Safecast/bGeigieZen/Misc documents  and software/SEO/What are the key benefits of using the bGeigieZen.pdf

The bGeigieZen offers several key benefits for educational settings:

These features make the bGeigieZen an excellent tool for enhancing STEM education and promoting hands-on, practical learning experiences in radiation monitoring and environmental science.

⁂

# What are the key benefits of using the bGeigieZen in educational settings

1. Practical learning tool: It serves as a hands-on device for teaching about radiation, nuclear science, and environmental monitoring in academic settings .
[1] [2]
2. Easy assembly: Students can build the device from a kit in about 30 minutes, providing a valuable learning experience in electronics and instrumentation .

[3]

3. Real-time data logging: The bGeigieZen can log radiation data in real-time using Wi-Fi, allowing students to collect and analyze environmental data quickly .

[3]

4. Open data sharing: It supports exporting data in formats compatible with Safecast's open data platforms, encouraging collaborative research and data analysis .

[1]

5. Versatile applications: The device can be used for various educational projects, from environmental monitoring to community science initiatives .

[1]

6. User-friendly interface: Its intuitive controls and clear IPS LCD display make it accessible to students of all experience levels .

[1]

7. Integration with online resources: Data can be easily visualized and interpreted using the Safecast API and online map, enhancing students' data analysis skills .

[3]

8. Customization potential: The open-source nature of the device allows for modification and integration into existing research infrastructures, promoting advanced learning opportunities .

[1]

9. Interdisciplinary learning: It combines elements of physics, environmental science, data analysis, and citizen science, fostering a multidisciplinary approach to education .
[1] [2]
10. Community engagement: The bGeigieZen can be used in community science projects, allowing students to participate in real-world environmental monitoring and contribute to collective safety data .

[1]

1. https://bgeigiezen.safecast.jp
2. https://safecast.org/devices/bgeigie-zen/

3. https://safecast.org/safecast-introduces-our-latest-open-source-geiger-counter-the-bgeigiezen/
