Safecast/bGeigieZen/Misc documents  and software/SEO/What role does the bGeigieZen play in educational.pdf

The bGeigieZen plays a significant role in educational programs at universities by serving as a versatile and practical tool for teaching and research in environmental science and radiation monitoring. Its contributions include:

By integrating the bGeigieZen into their educational programs, universities empower students with practical skills and contribute to broader scientific efforts in radiation safety and environmental stewardship.

⁂

# What role does the bGeigieZen play in educational programs at universities

1. Hands-on Learning: The bGeigieZen is used in laboratory courses where students can assemble the device from a kit, gaining practical experience in electronics, instrumentation, and radiation detection.
2. Teaching Radiation Science: It provides a tangible way to teach concepts of radiation, nuclear science, and environmental monitoring, making abstract theories more accessible through real-world applications.
3. Fieldwork and Data Collection: With its GPS integration and real-time data logging capabilities, the device allows students to conduct field studies, collect radiation data, and map environmental conditions.
4. Interdisciplinary Applications: The bGeigieZen supports interdisciplinary learning by combining elements of physics, environmental science, data analysis, and citizen science into academic programs.
5. Open-Source Collaboration: Universities can leverage Safecast's open-source platform to share data and collaborate on global environmental monitoring projects, fostering a sense of community-driven science.
6. Research Projects: It is used in university-led research initiatives, such as studying radioactive contamination or assessing environmental safety around nuclear facilities.
7. Curriculum Integration: The device is incorporated into courses and workshops focused on environmental monitoring, promoting active learning and critical thinking among students.
