Safecast/bGeigieZen/Misc documents  and software/bGeigieZen  info.docx

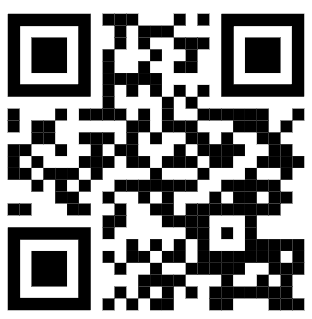
[picture p9: figure]

bGeigieZen information:

Version :V4.0.6

ID :5053

For more information visit

https://t.ly/_J40M
