Safecast/bGeigieZen/Misc documents  and software/safecast QR code sticker.docx

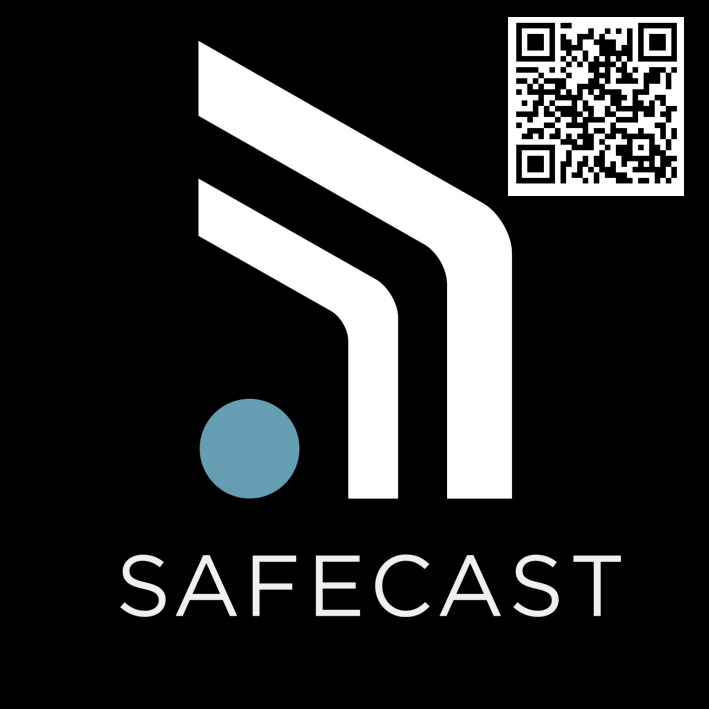
[picture p10: figure]
