Safecast/bGeigieZen/Misc documents  and software/2024-03-05 Zen sticker for brother QL700 between liner and case..docx

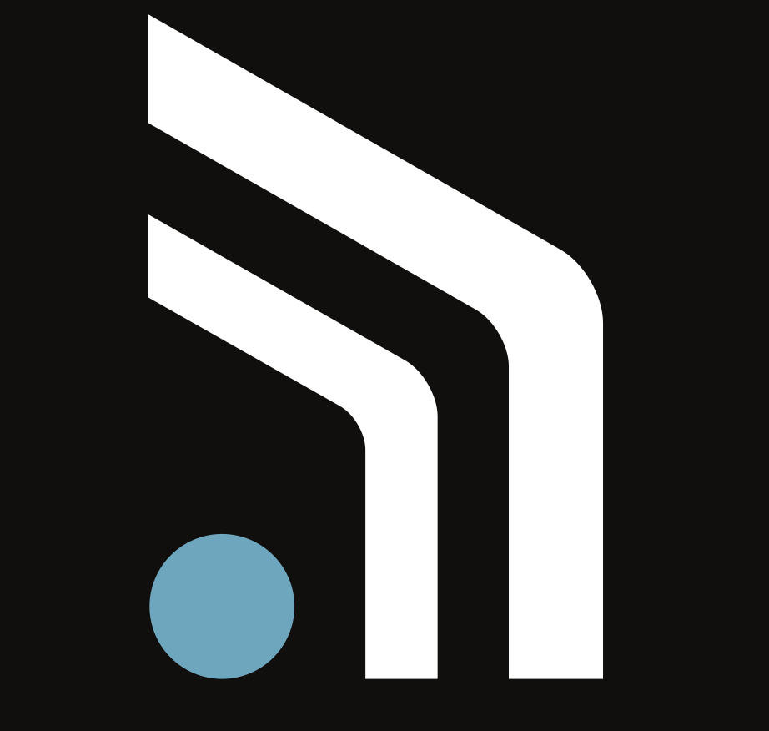
[picture p11: figure]
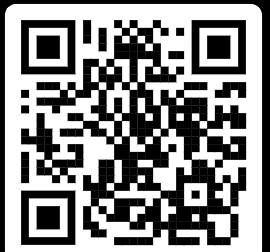
[picture p12: figure]

SAFECAST
