Safecast/bGeigieZen/Misc documents  and software/2024-03-05 Zen inside lines.docx

〒633-1302 奈良

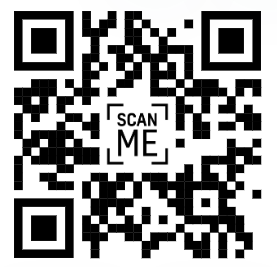
[picture p13: figure]

県宇陀郡御杖村菅野616

616 Sugano, (https://www.google.com/maps/place/YR-DESIGN/@34.482597,136.163349,4319m/data=!3m1!1e3!4m5!3m4!1s0x0:0x89b70d0ed6831661!8m2!3d34.482597!4d136.163349)

Mitsue-Village, Uda District, Nara, 633-1302 Japan (https://www.google.com/maps/place/YR-DESIGN/@34.482597,136.163349,4319m/data=!3m1!1e3!4m5!3m4!1s0x0:0x89b70d0ed6831661!8m2!3d34.482597!4d136.163349)
