Safecast/bGeigieZen/Misc documents  and software/SEO/How can universities integrate the bGeigieZen into.pdf

Universities can integrate the bGeigieZen into their environmental monitoring programs in several effective ways:

# How can universities integrate the bGeigieZen into their environmental monitoring programs

Research Projects

1. Conduct long-term radiation monitoring studies across campus and surrounding areas, creating detailed radiation maps over time .
[1] [2]
2. Use the device in interdisciplinary research projects combining environmental science, physics, and data analysis.

Curriculum Integration

1. Incorporate the bGeigieZen into laboratory courses for hands-on experience with radiation detection and environmental monitoring .

[2]

2. Develop practical exercises where students assemble the device from a kit, enhancing their understanding of instrumentation .

[1]

Community Science Initiatives

1. Engage students in citizen science projects, contributing data to Safecast's open platforms and fostering community involvement .

[2]

2. Collaborate with local communities to monitor radiation levels, promoting environmental awareness and stewardship.

Data Analysis and Visualization

1. Utilize the bGeigieZen's real-time data logging capabilities to teach students about data collection, analysis, and interpretation .

[1]

2. Integrate collected data with the Safecast API and online map for advanced data visualization exercises .

[1]

Emergency Preparedness

1. Include the bGeigieZen in emergency response training programs for campus safety personnel .

[2]

2. Establish a network of fixed bGeigieZen sensors across campus for continuous environmental monitoring .

[1]

By implementing these strategies, universities can leverage the bGeigieZen's capabilities to enhance their environmental monitoring programs, providing students with valuable hands-on experience and contributing to broader scientific understanding of radiation levels in their local environment.

⁂

1. https://safecast.org/safecast-introduces-our-latest-open-source-geiger-counter-the-bgeigiezen/
2. https://safecast.org/devices/bgeigie-zen/
