Safecast/bGeigieZen/bgeigie_firmware_pio/images/Screenshot from 2022-03-10 14-36-16 Robin sample wifi implementaion.png

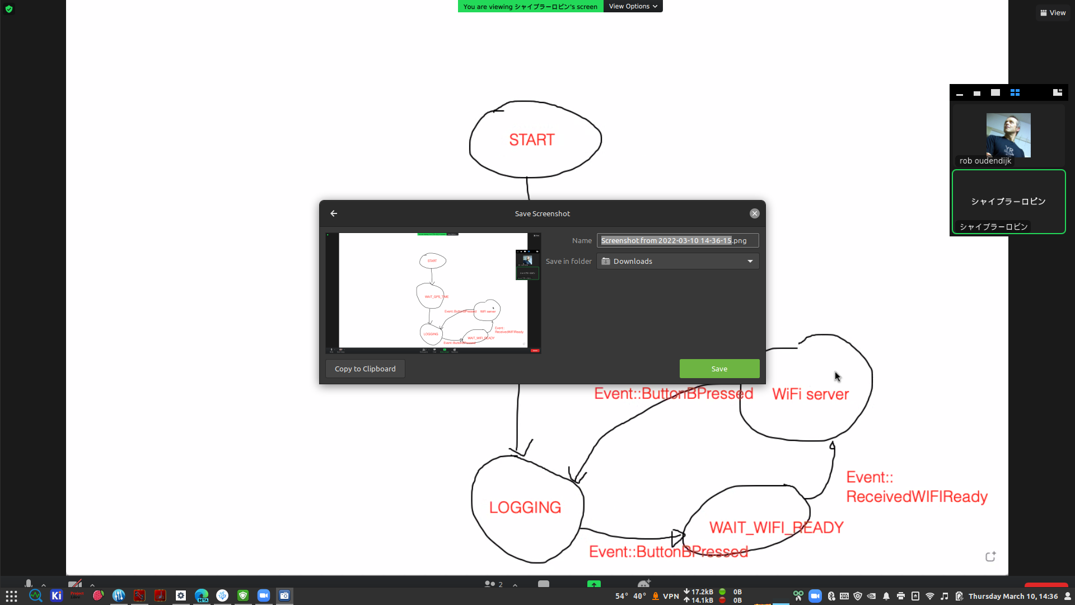
bgeigie_firmware_pio/images/Screenshot from 2022-03-10 14-36-16 Robin sample wifi implementaion.png
