Safecast/bGeigieZen/designs/concept.png

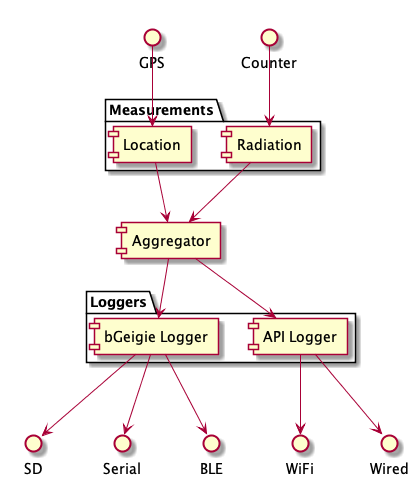
designs/concept.png
