Safecast/bGeigieZen/designs/design_idea.png

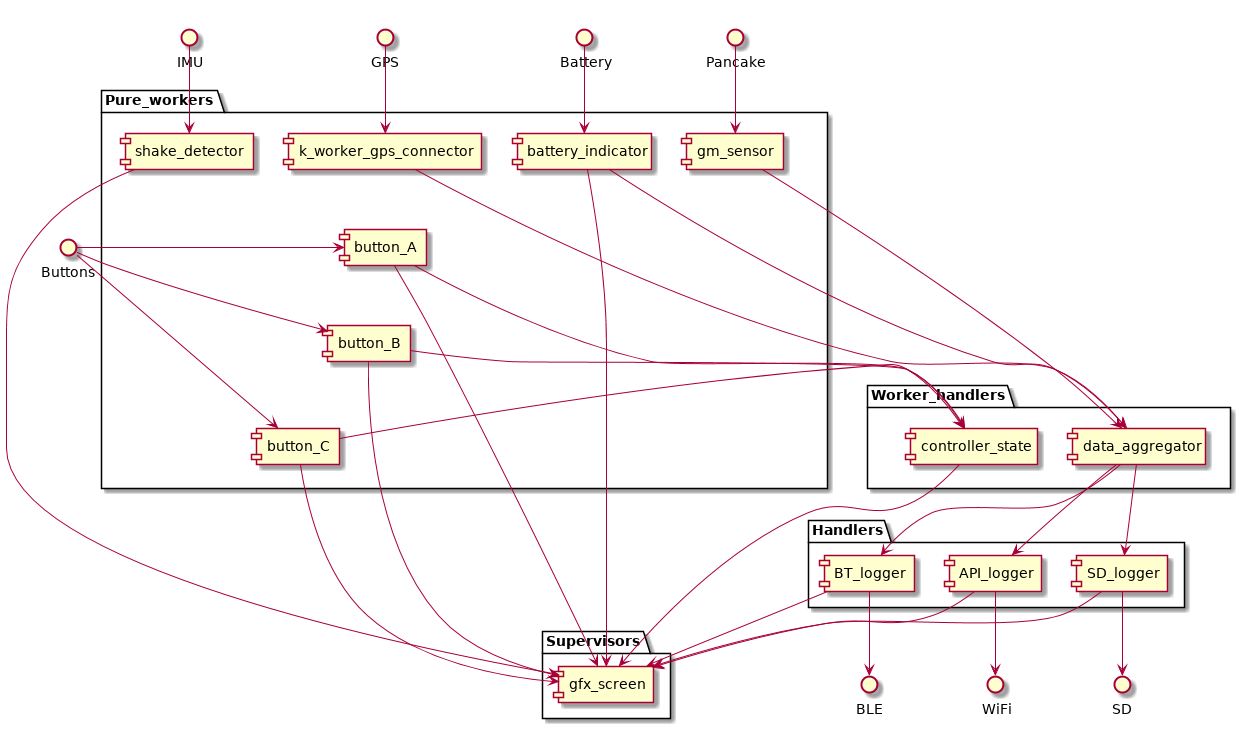
designs/design_idea.png
