Safecast/bGeigieZen/designs/Idea for rotating text.png

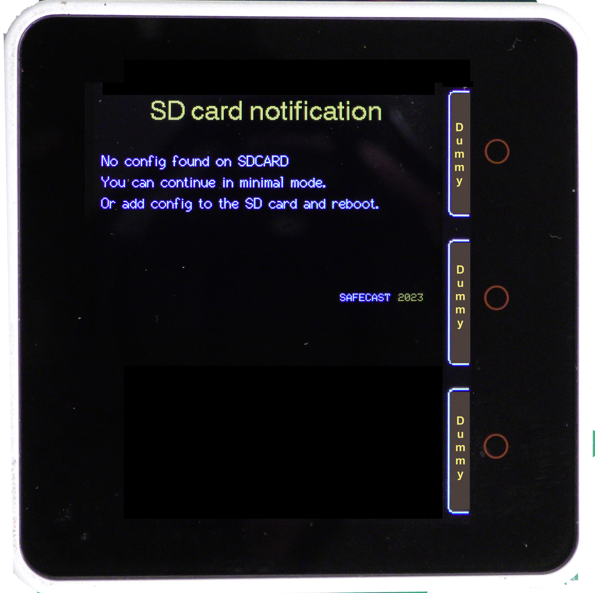
designs/Idea for rotating text.png
