Safecast/bGeigieZen/Misc documents  and software/436710781_377460041415420_154169997321250752_n.jpg

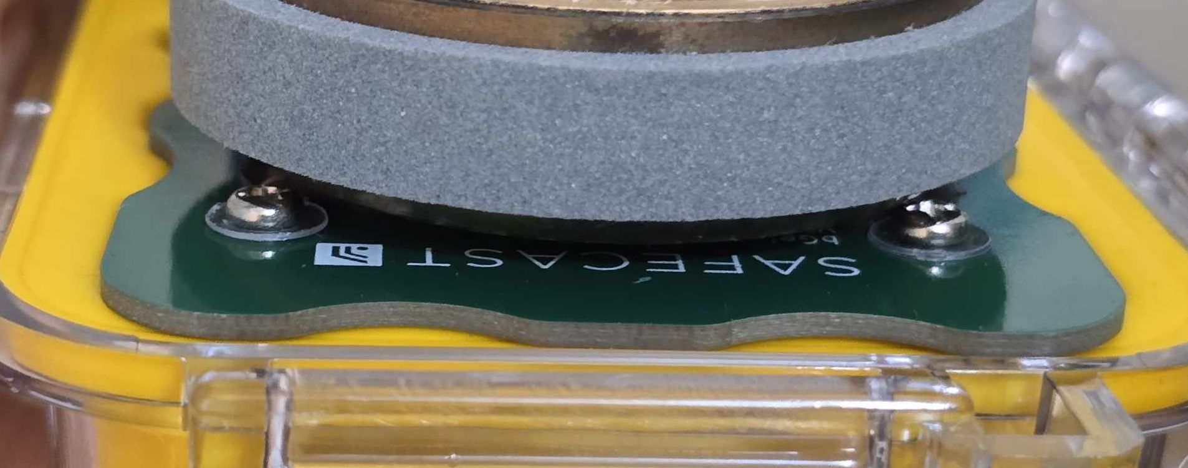
Misc documents and software/436710781_377460041415420_154169997321250752_n.jpg
