Safecast/bGeigieZen/Misc documents  and software/buttons sticker Zen.png

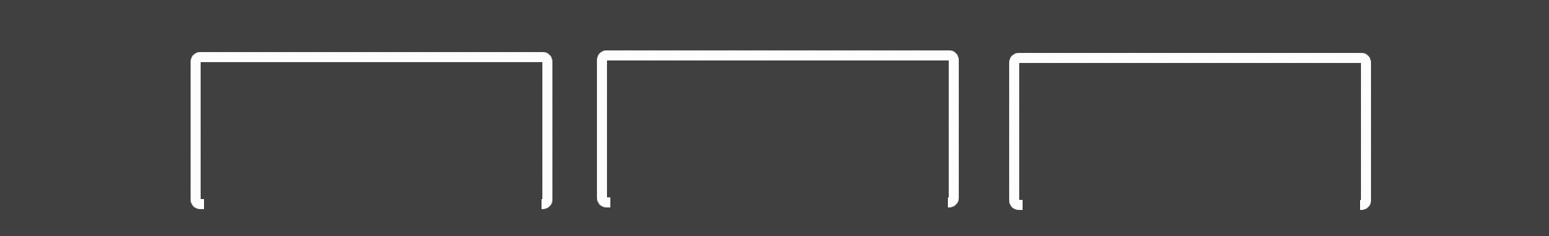
Misc documents and software/buttons sticker Zen.png
