Safecast/bGeigieZen/Misc documents  and software/Editor _ Mermaid Chart-2025-06-17-123522.png

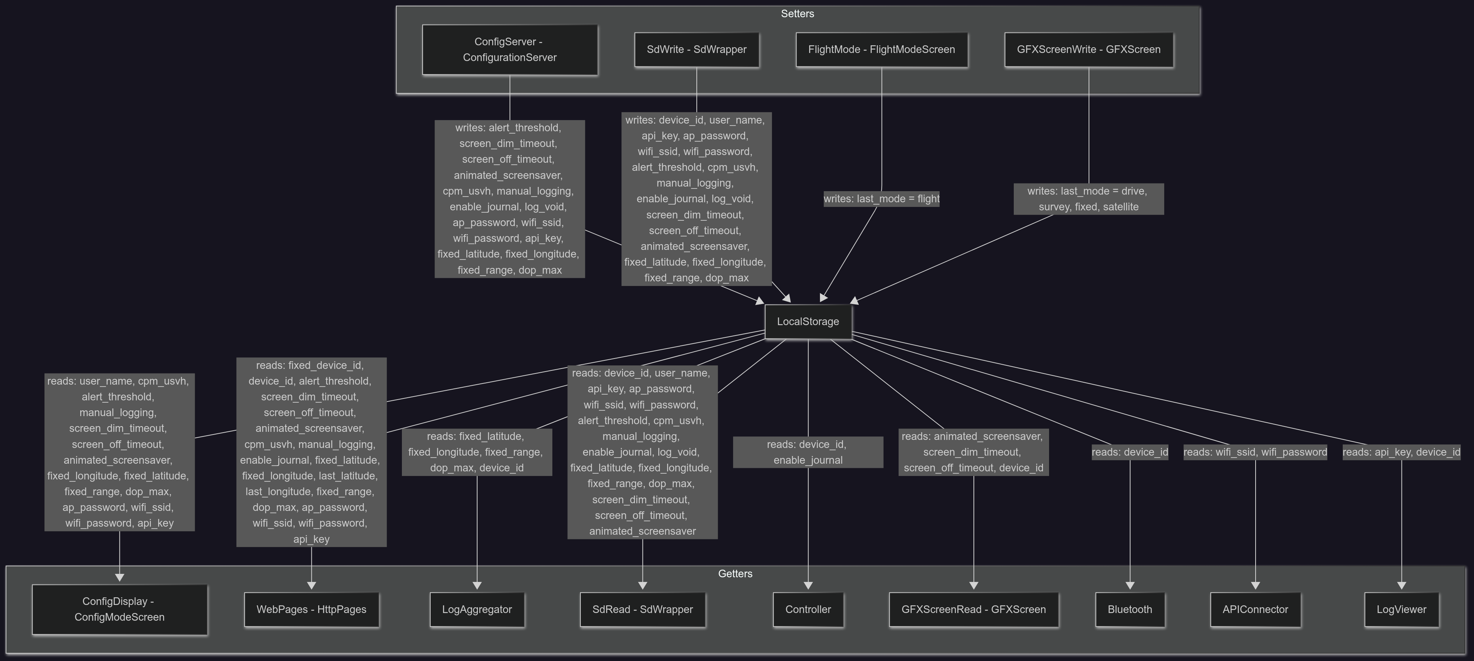
Misc documents and software/Editor _ Mermaid Chart-2025-06-17-123522.png
