Safecast/bGeigieZen/Misc documents  and software/Editor _ Mermaid Chart-2025-06-18-021637.png

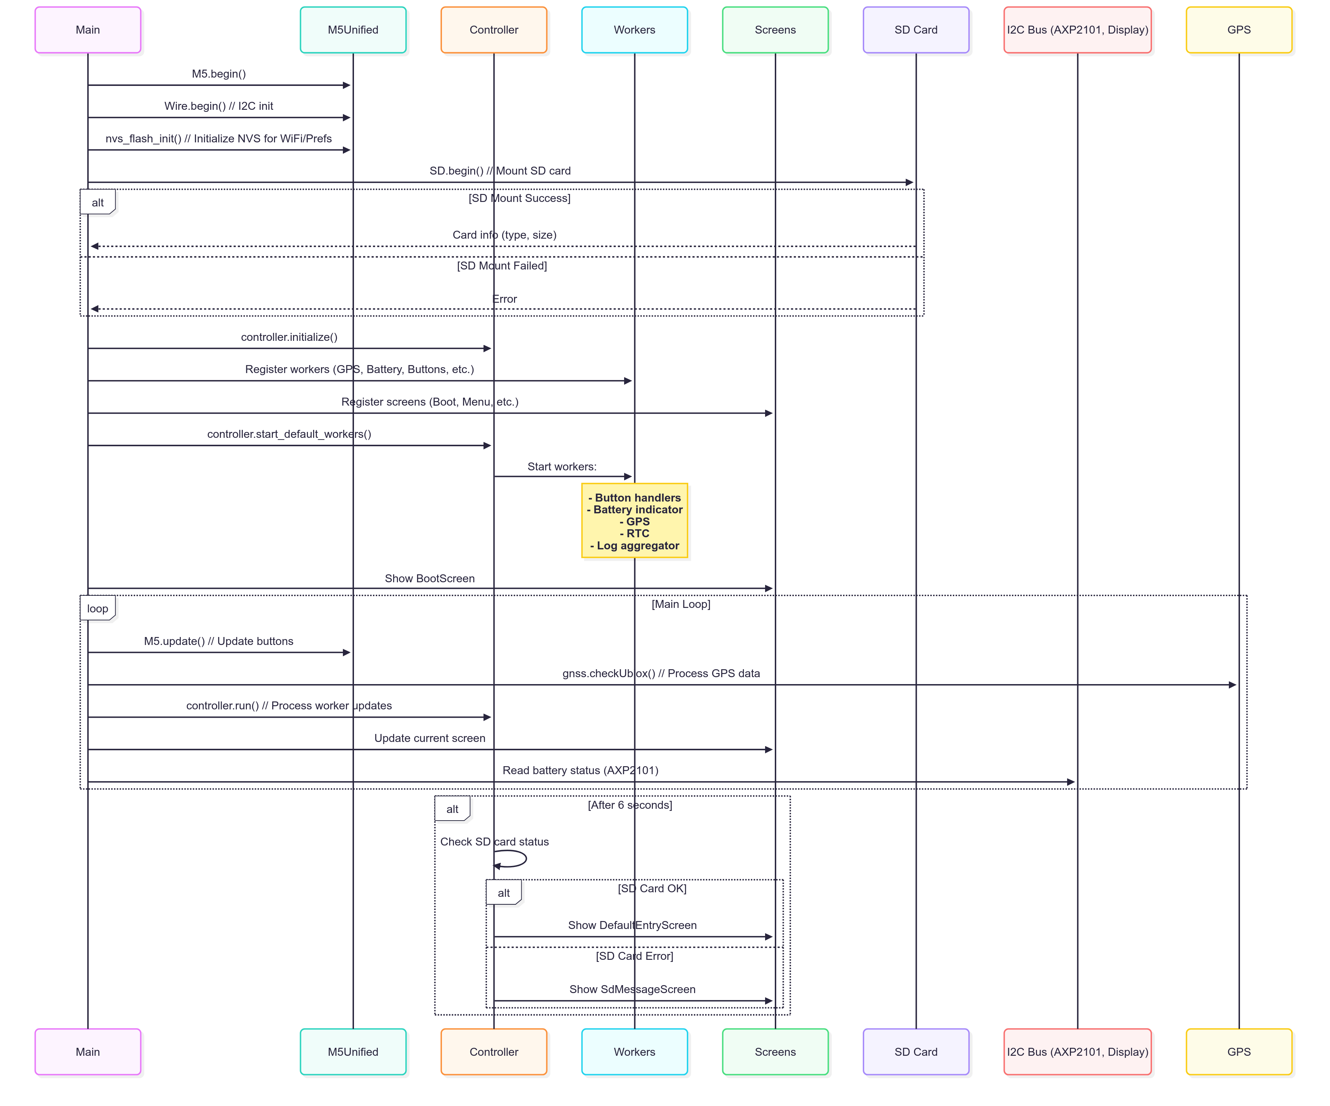
Misc documents and software/Editor _ Mermaid Chart-2025-06-18-021637.png
