Safecast/bGeigieZen/Misc documents  and software/Images /3006.jpg

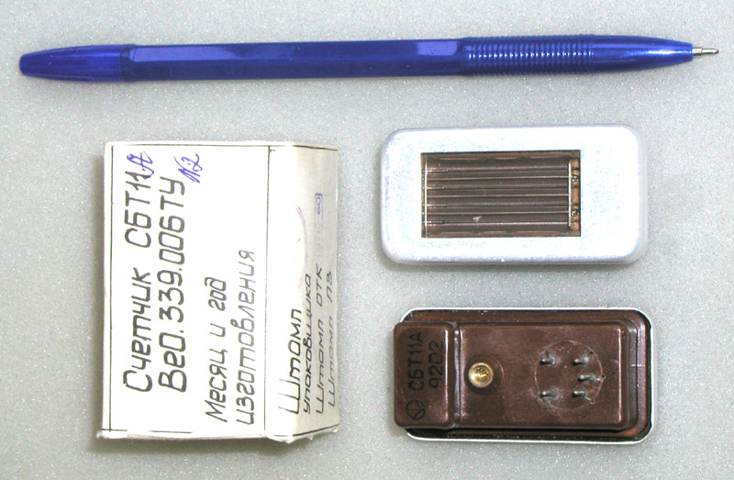
Misc documents and software/Images /3006.jpg
