Safecast/bGeigieZen/Misc documents  and software/Images /3006_1.gif

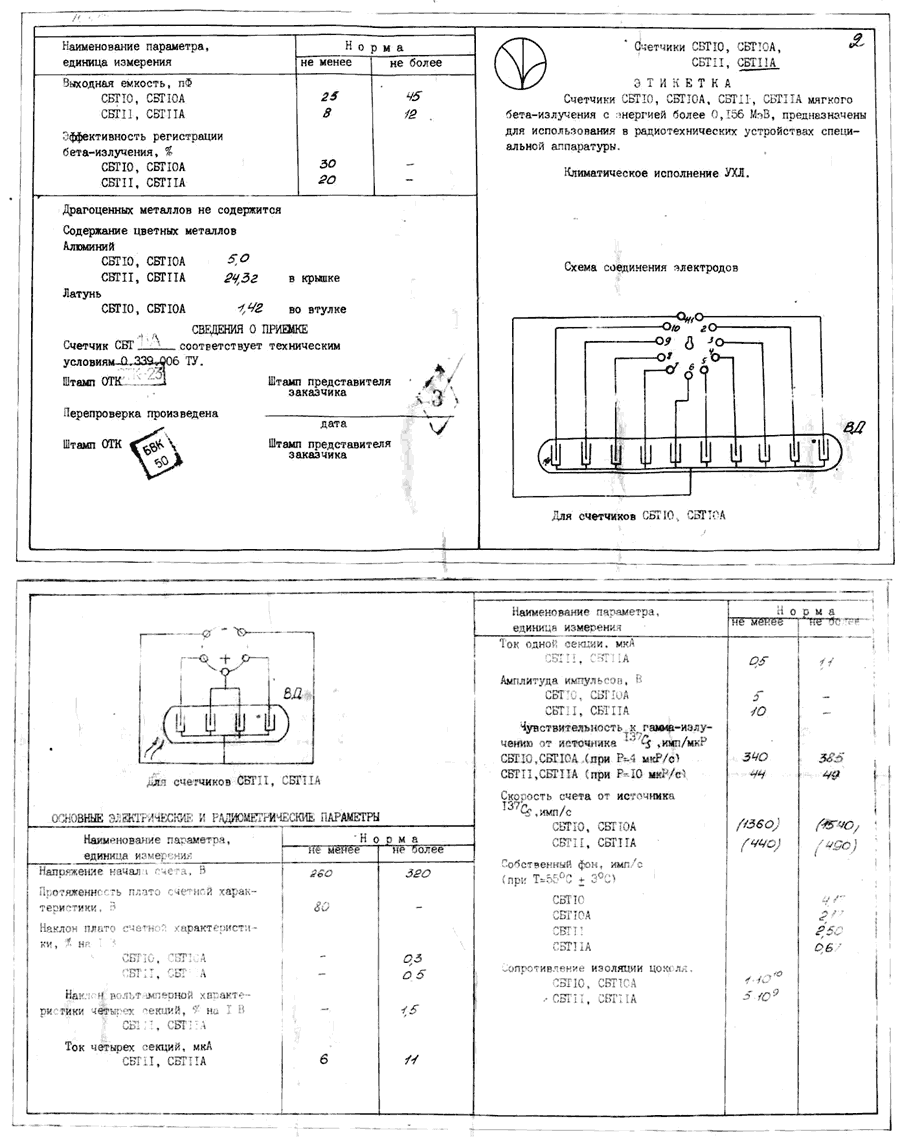
Misc documents and software/Images /3006_1.gif
