Safecast/bGeigieZen/Misc documents  and software/Images /SBT-11A data sheet.jpg

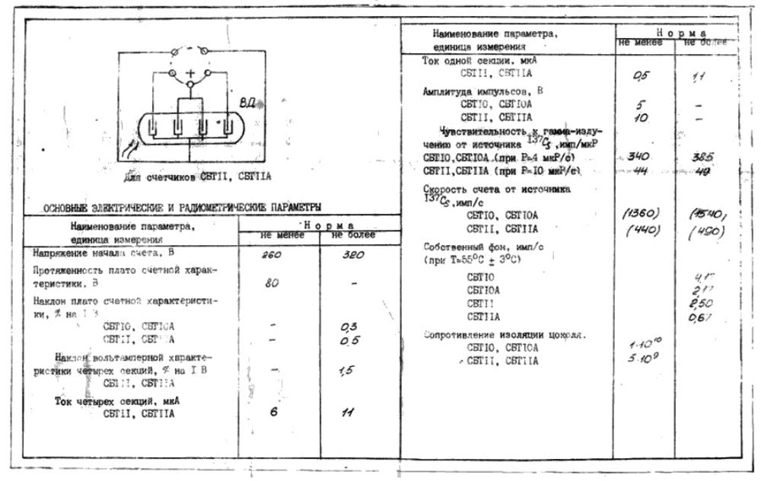
Misc documents and software/Images /SBT-11A data sheet.jpg
