Safecast/bGeigieZen/Misc documents  and software/Images/Screenshot from 2024-03-13 09-20-50.png

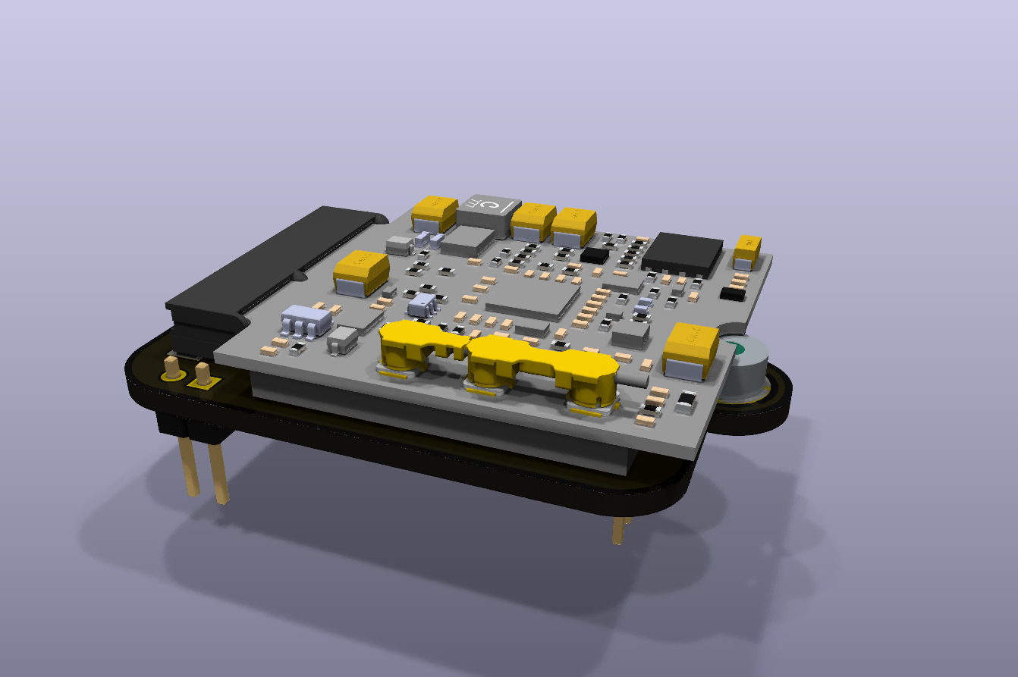
Misc documents and software/Images/Screenshot from 2024-03-13 09-20-50.png
