Safecast/bGeigieZen/Misc documents  and software/Images/Screenshot from 2024-03-13 09-23-09.png

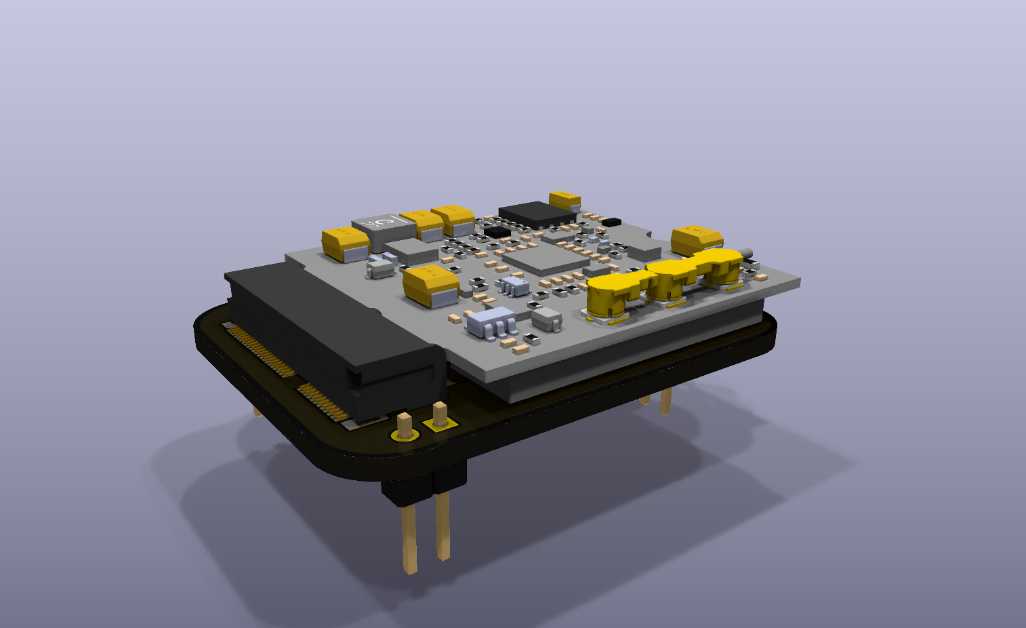
Misc documents and software/Images/Screenshot from 2024-03-13 09-23-09.png
