Safecast/bGeigieZen/Misc documents  and software/IMG_1486.jpg

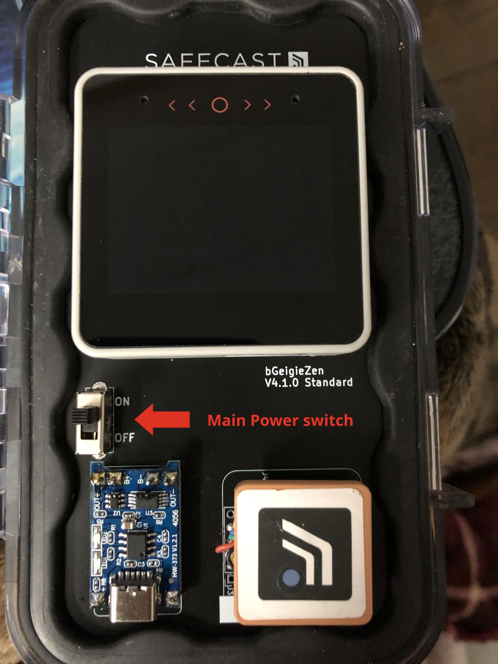
Misc documents and software/IMG_1486.jpg
