Safecast/bGeigieZen/Misc documents  and software/IMG_1487.jpg

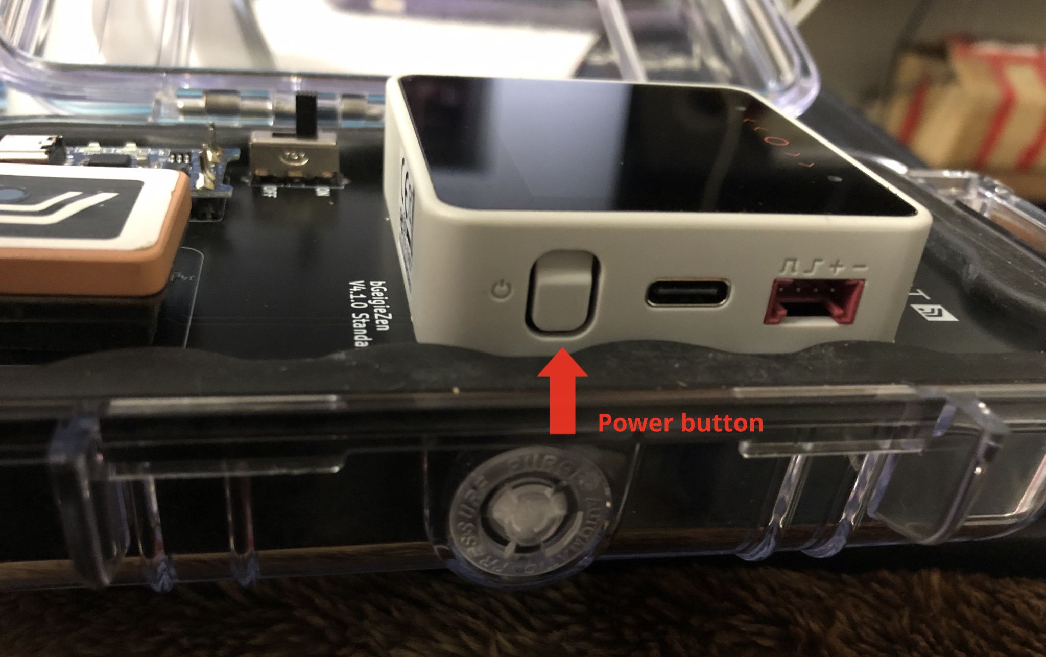
Misc documents and software/IMG_1487.jpg
