Safecast/bGeigieZen/Misc documents  and software/IMG_1488.jpg

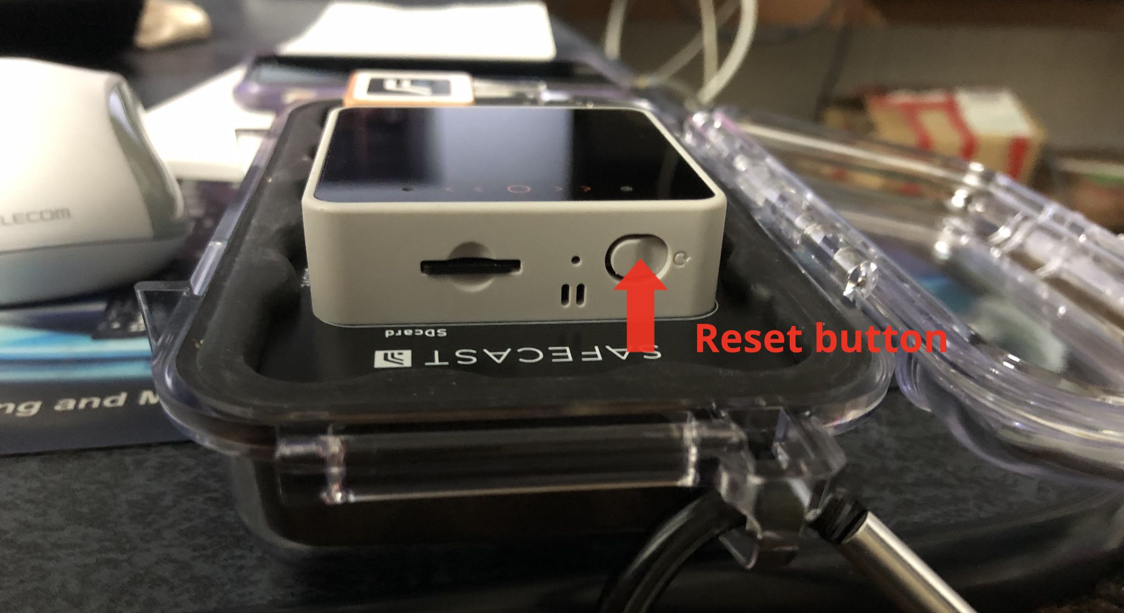
Misc documents and software/IMG_1488.jpg
