Safecast/bGeigieZen/Misc documents  and software/LND 7317 grids invoice from Louis.png

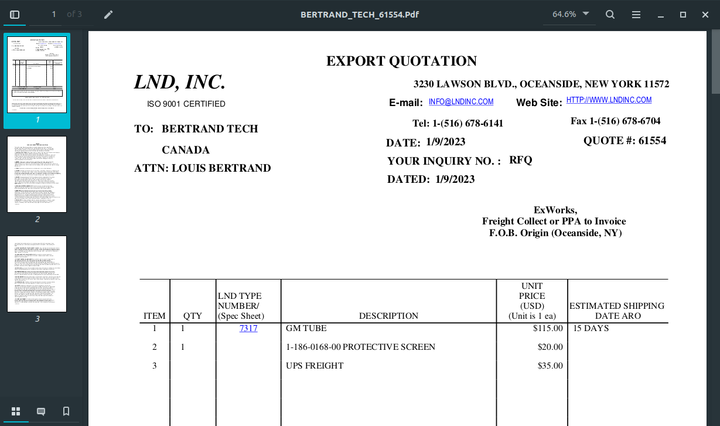
Misc documents and software/LND 7317 grids invoice from Louis.png
