Safecast/bGeigieZen/Misc documents  and software/Vertical timeline nano-zen.png

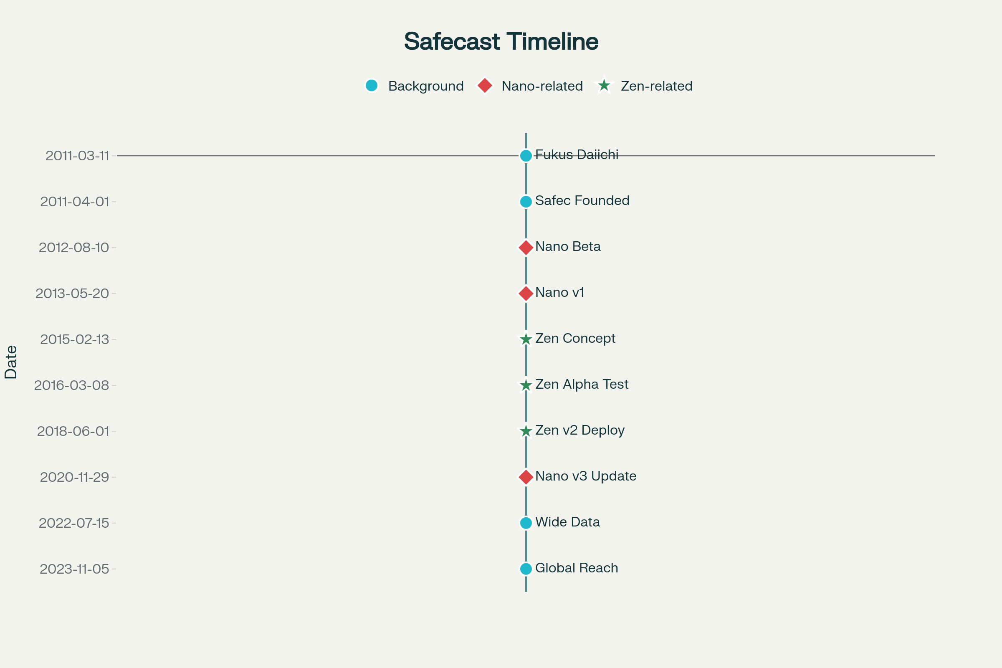
Misc documents and software/Vertical timeline nano-zen.png
