Safecast/bGeigieZen/Misc documents  and software/3d models/pelican 1040-cradle slide mold.stl

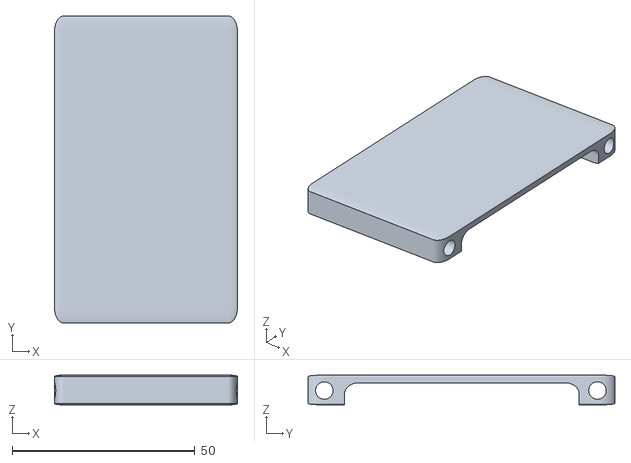
[picture p49: CAD file, 2024-11-16]
Misc documents and software/3d models/pelican 1040-cradle slide mold.stl
50.1 x 84.0 x 8.17
