Safecast/bGeigieZen/hardware/bGeigieZen V4.x.x draft and production/bGeigieZen V4.2.x/ GPS for  4.1.0 aNFW .stl

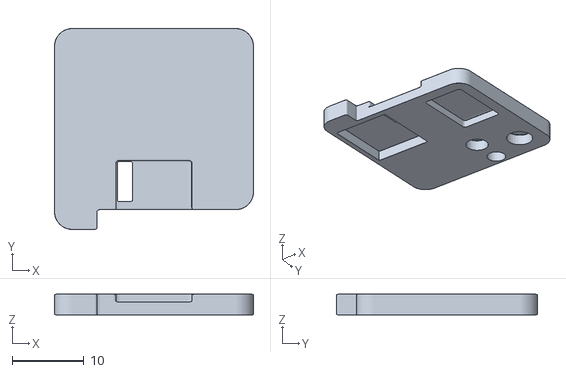
[picture p50: CAD file, 2024-12-10]
hardware/bGeigieZen V4.x.x draft and production/bGeigieZen V4.2.x/ GPS for 4.1.0 aNFW .stl
27.8 x 28.1 x 2.87
