Safecast/bGeigieZen/hardware/bGeigieZen V4.x.x draft and production/bGeigieZen V4.2.x/shapes3D/3557-2.step

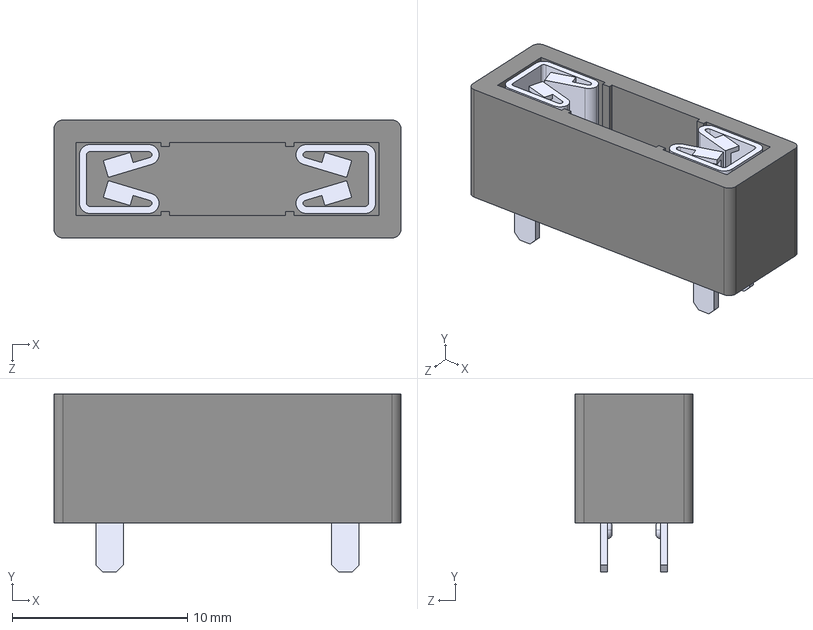
[picture p51: CAD file, 2024-08-04]
hardware/bGeigieZen V4.x.x draft and production/bGeigieZen V4.2.x/shapes3D/3557-2.step
19.8 x 10.2 x 6.73 mm
