Safecast/bGeigieZen/Misc documents  and software/3d models/pelican 1040-cradle making case mold-2b.stl

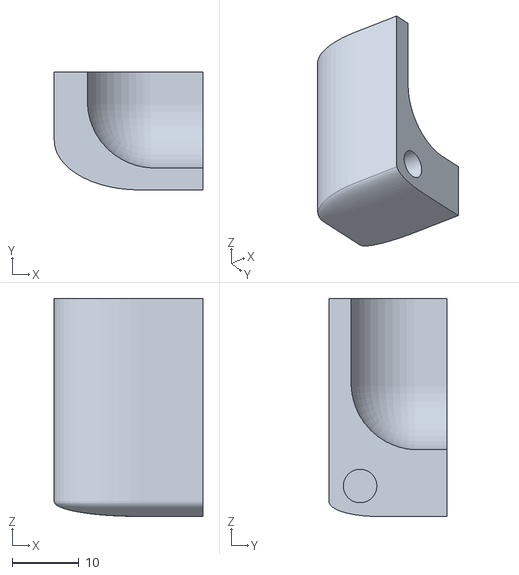
[picture p52: CAD file, 2024-10-24]
Misc documents and software/3d models/pelican 1040-cradle making case mold-2b.stl
22.2 x 17.6 x 32.6
