Safecast/bGeigieZen/hardware/bGeigieZen V4.x.x draft and production/bGeigieZen V4.2.x/ GPS for  4.0.9 NFW .stl

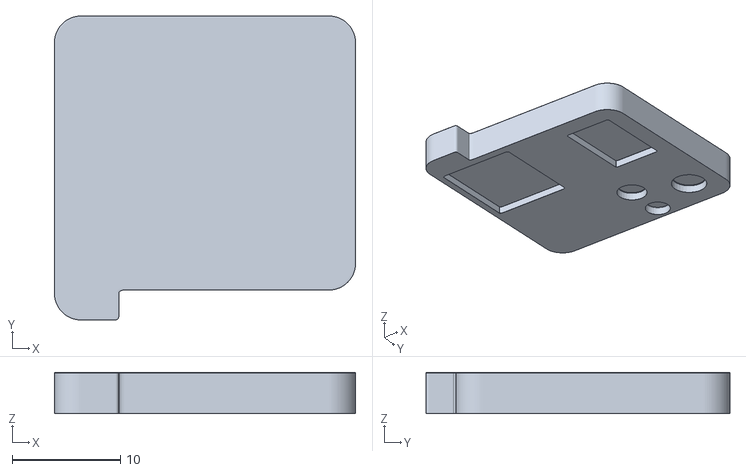
[picture p53: CAD file, 2024-12-10]
hardware/bGeigieZen V4.x.x draft and production/bGeigieZen V4.2.x/ GPS for 4.0.9 NFW .stl
27.8 x 28.1 x 3.79
