Safecast/bGeigieZen/Misc documents  and software/3d models/pelican 1040-cradle QI sled A.stl

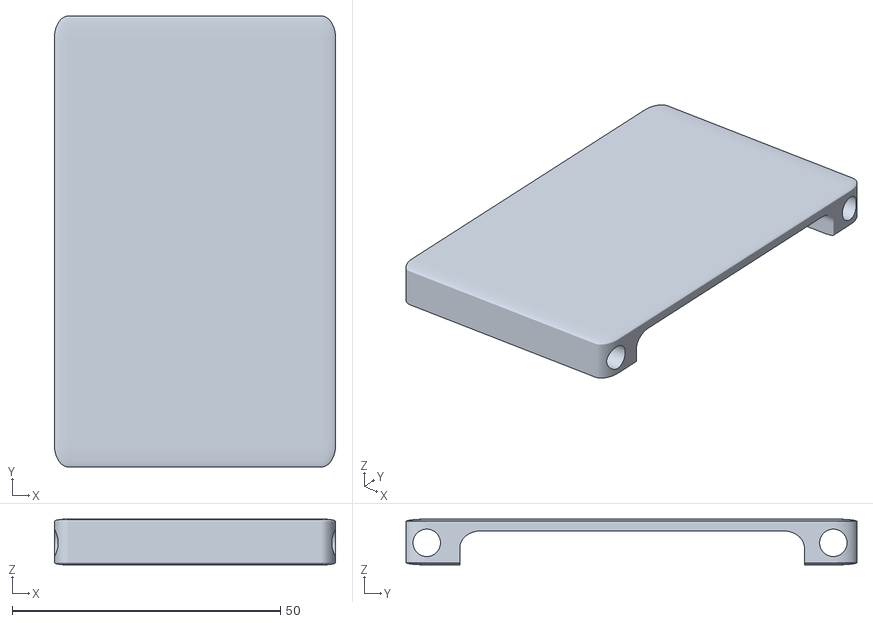
[picture p54: CAD file, 2024-10-24]
Misc documents and software/3d models/pelican 1040-cradle QI sled A.stl
52.4 x 84.0 x 8.55
