Safecast/bGeigieZen/hardware/bGeigieZen V4.x.x draft and production/bGeigieZen V4.2.x/shapes3D/Charging Module TP4057 Mini.step

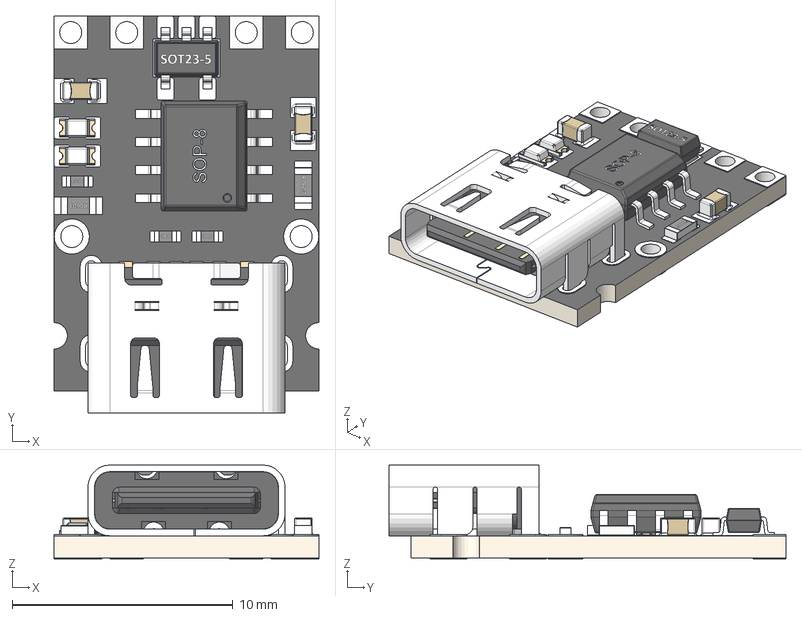
[picture p55: CAD file, 2024-05-21]
hardware/bGeigieZen V4.x.x draft and production/bGeigieZen V4.2.x/shapes3D/Charging Module TP4057 Mini.step
12.0 x 18.0 x 4.26 mm
USB C 6P SMD Female
SOP-8
0603LEDO
0603LEDR
Pin1 x 2
Pin2 x 2
CeramicBody x 2
SOT23-5 V1
R0603 x 2
R0402 x 3
