Safecast/bGeigieZen/Misc documents  and software/3d models/pelican 1040-cradle making case mold-2a.stl

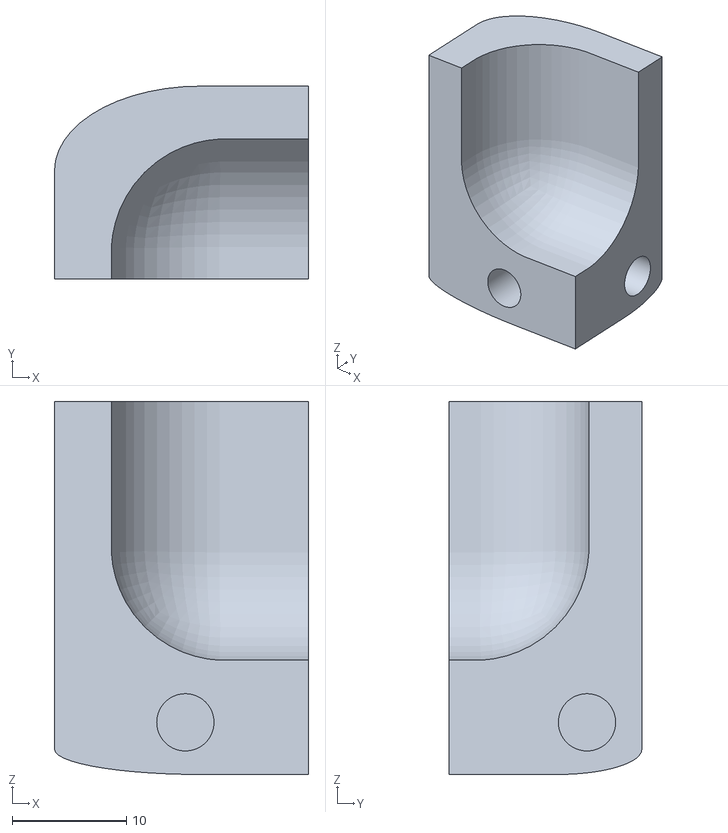
[picture p56: CAD file, 2024-10-24]
Misc documents and software/3d models/pelican 1040-cradle making case mold-2a.stl
22.2 x 16.8 x 32.6
