Safecast/bGeigieZen/Misc documents  and software/3d models/pelican 1040-cradle making case mold-2d.stl

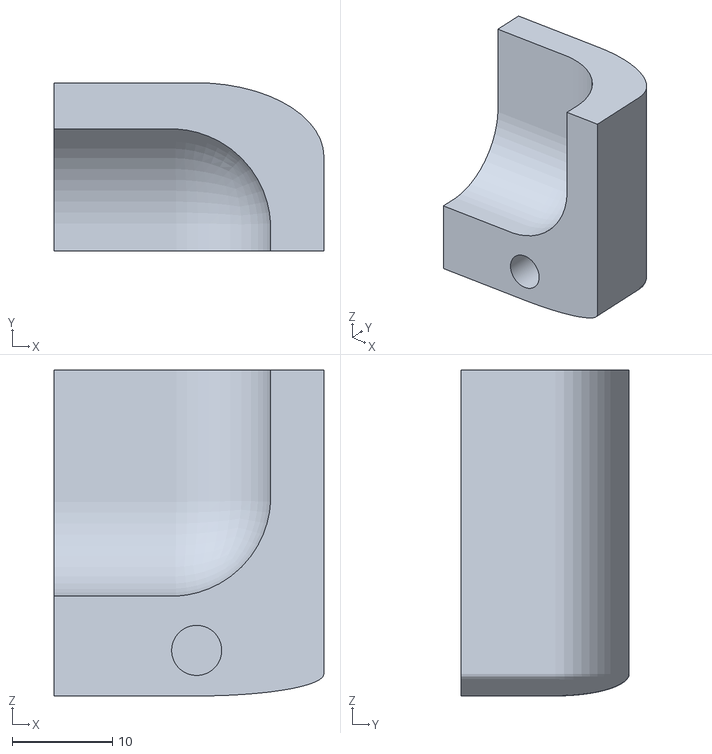
[picture p59: CAD file, 2024-10-24]
Misc documents and software/3d models/pelican 1040-cradle making case mold-2d.stl
27.0 x 16.8 x 32.6
