Safecast/bGeigieZen/hardware/bGeigieZen V4.x.x draft and production/bGeigieZen V4.2.x/shapes3D/LIGHT_UNIT.stp

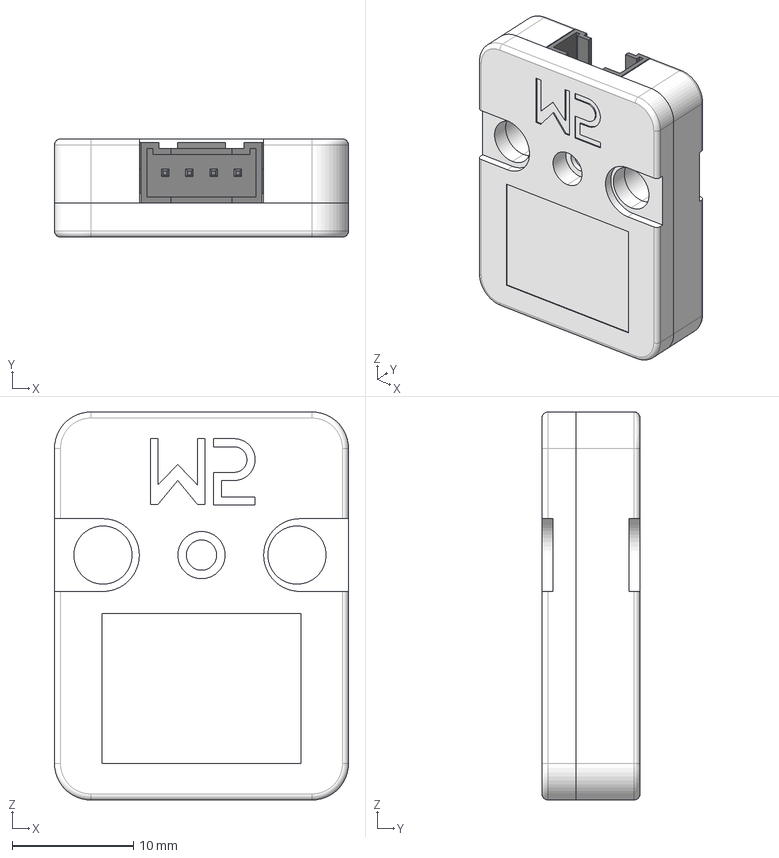
[picture p60: CAD file, 2023-09-07]
hardware/bGeigieZen V4.x.x draft and production/bGeigieZen V4.2.x/shapes3D/LIGHT_UNIT.stp
24.2 x 8.10 x 32.0 mm
M5STACK_LIGHT_UNIT-prt0
M5STACK_LIGHT_UNIT-prt1
M5STACK_LIGHT_UNIT-prt2
M5STACK_LIGHT_UNIT-prt3
M5STACK_LIGHT_UNIT-prt4
M5STACK_LIGHT_UNIT-prt5
M5STACK_LIGHT_UNIT-prt6
M5STACK_LIGHT_UNIT-prt7
M5STACK_LIGHT_UNIT-prt8
