Safecast/bGeigieZen/Misc documents  and software/3d models/plate core1 for NFW and standard.stl

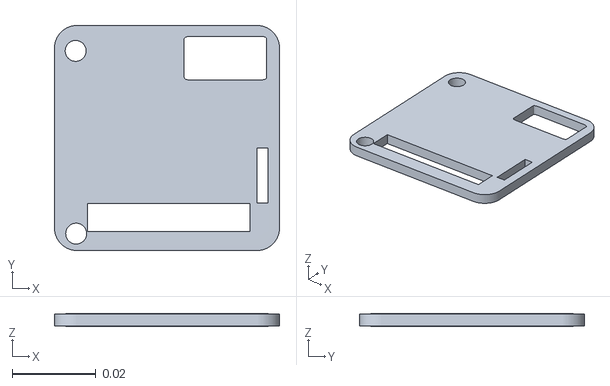
[picture p61: CAD file, 2024-10-21]
Misc documents and software/3d models/plate core1 for NFW and standard.stl
0.0538 x 0.0538 x 0.003
