Safecast/bGeigieZen/hardware/bGeigieZen V4.x.x draft and production/bGeigieZen V4.2.x/shapes3D/qwiic.STEP

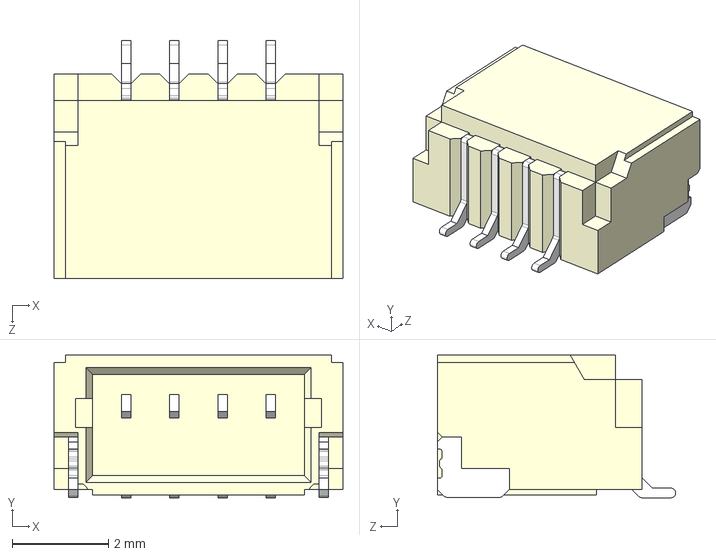
[picture p62: CAD file, 2022-01-05]
hardware/bGeigieZen V4.x.x draft and production/bGeigieZen V4.2.x/shapes3D/qwiic.STEP
6.00 x 2.96 x 4.95 mm
