Safecast/bGeigieZen/Misc documents  and software/3d models/Zen cradle rought making case.stl

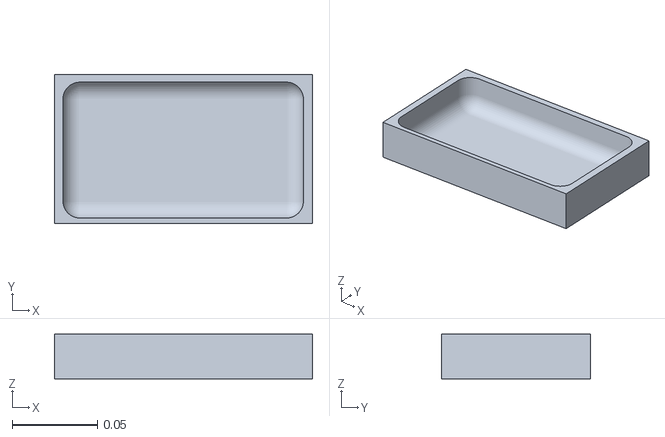
[picture p63: CAD file, 2024-10-21]
Misc documents and software/3d models/Zen cradle rought making case.stl
0.151 x 0.0877 x 0.0262
