Safecast/bGeigieZen/hardware/bGeigieZen V4.x.x draft and production/bGeigieZen V4.2.x/shapes3D/QWIIC-SM04B-SRSS-TB(LF)(SN).stl

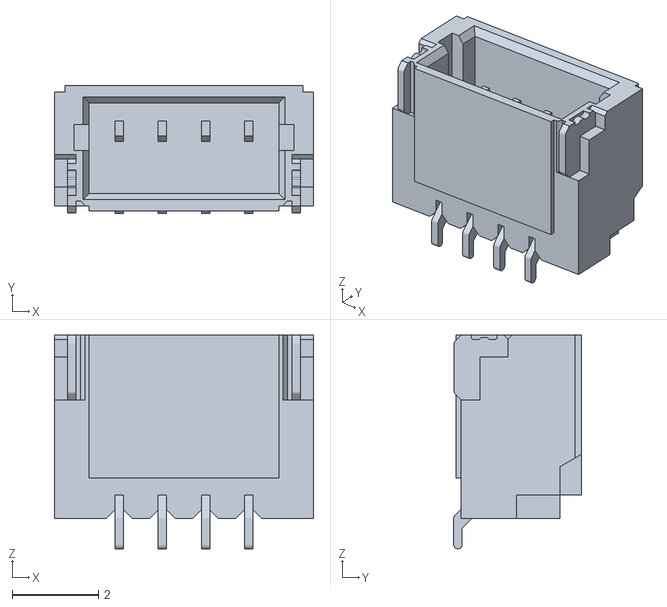
[picture p64: CAD file, 2022-01-05]
hardware/bGeigieZen V4.x.x draft and production/bGeigieZen V4.2.x/shapes3D/QWIIC-SM04B-SRSS-TB(LF)(SN).stl
6.00 x 2.96 x 4.95
