Safecast/bGeigieZen/Misc documents  and software/3d models/pelican 1043-cradle making case 1.stl

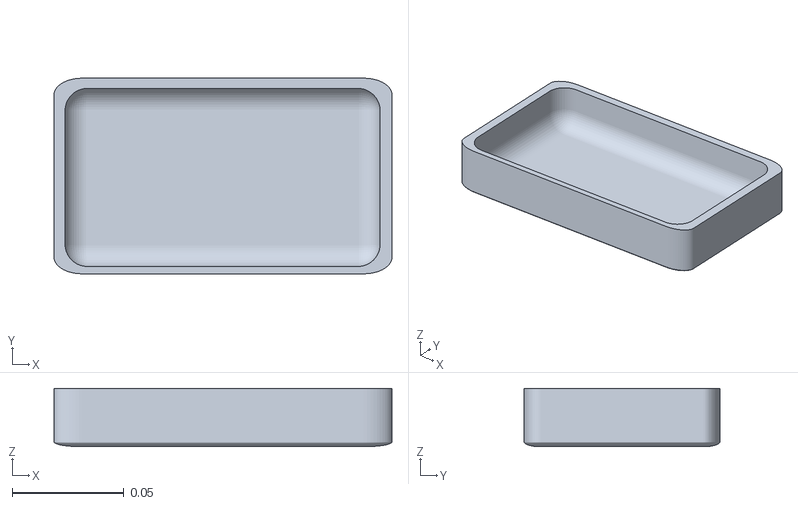
[picture p65: CAD file, 2024-10-21]
Misc documents and software/3d models/pelican 1043-cradle making case 1.stl
0.151 x 0.0877 x 0.0262
