Safecast/bGeigieZen/Misc documents  and software/3d models/pelican 1040-cradle QI sled and sides.stl

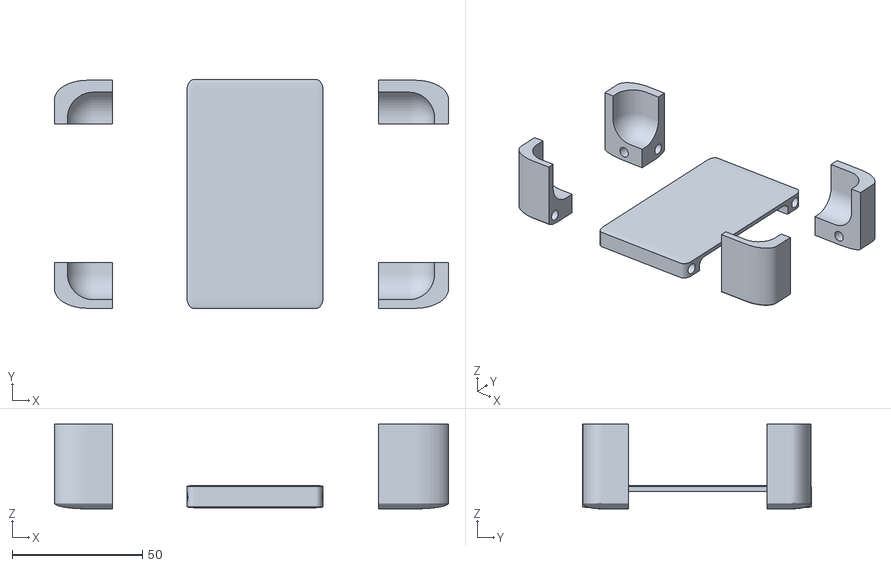
[picture p67: CAD file, 2024-10-21]
Misc documents and software/3d models/pelican 1040-cradle QI sled and sides.stl
151.4 x 87.9 x 32.6
