Safecast/bGeigieZen/Misc documents  and software/3d models/pelican 1040-1 case.stl

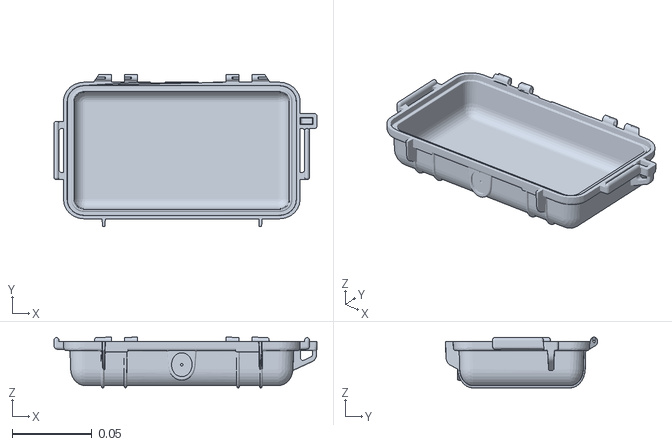
[picture p68: CAD file, 2024-10-21]
Misc documents and software/3d models/pelican 1040-1 case.stl
0.165 x 0.0955 x 0.032
