Safecast/bGeigieZen/Misc documents  and software/3d models/plate core one for NFW and standard.stl

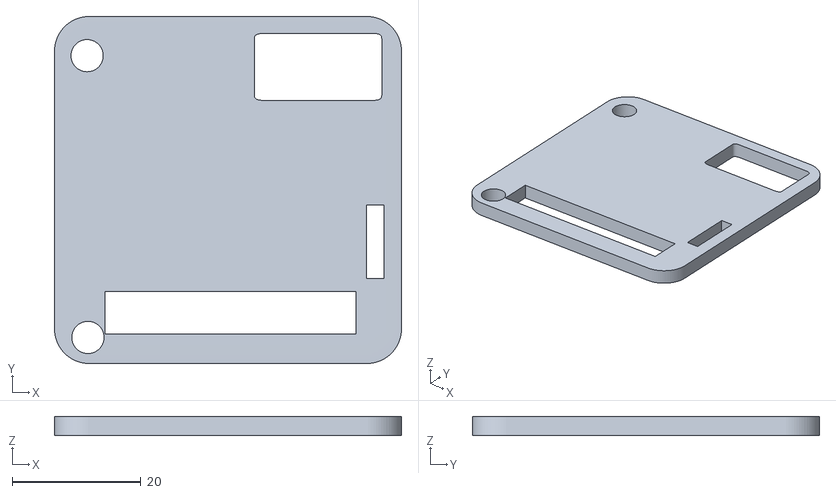
[picture p69: CAD file, 2024-10-21]
Misc documents and software/3d models/plate core one for NFW and standard.stl
53.8 x 53.8 x 3.00
