Safecast/bGeigieZen/Misc documents  and software/3d models/pelican 1040-cradle making case mold-2.stl

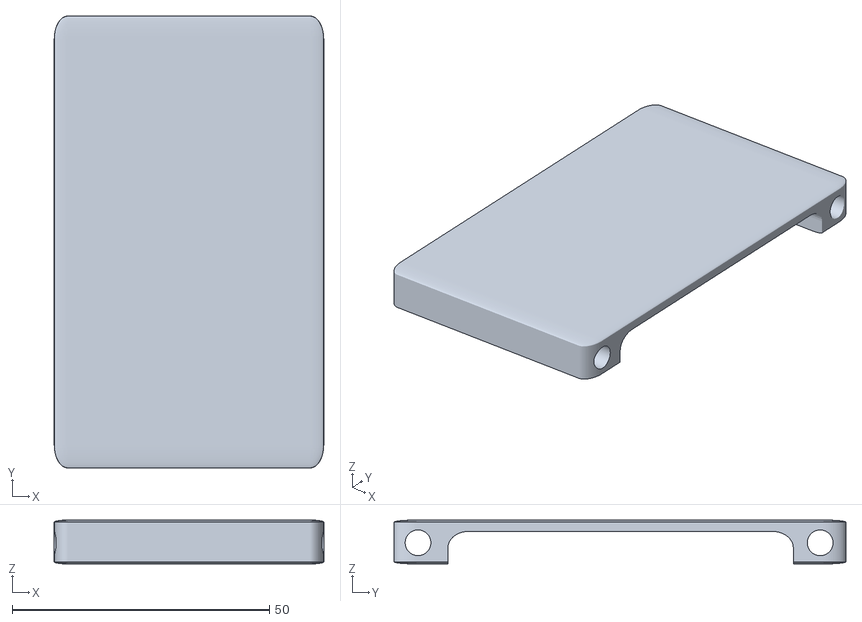
[picture p70: CAD file, 2024-10-21]
Misc documents and software/3d models/pelican 1040-cradle making case mold-2.stl
52.4 x 87.9 x 8.55
