Safecast/bGeigieZen/Misc documents  and software/3d models/pelican 1040-cradle QI sides.stl

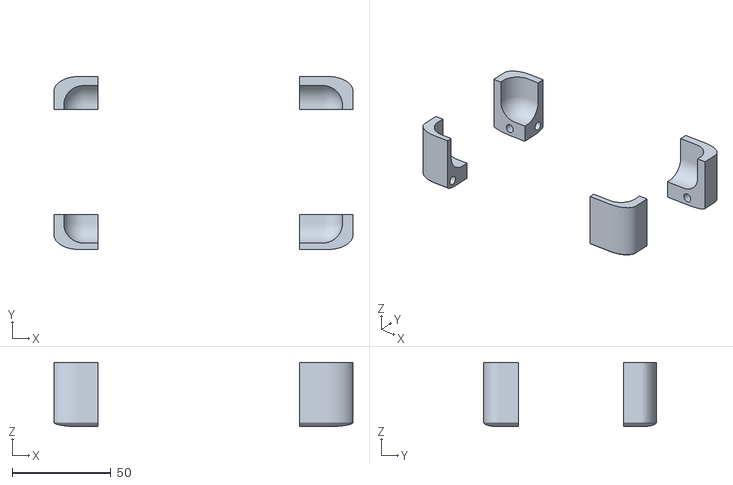
[picture p71: CAD file, 2024-10-21]
Misc documents and software/3d models/pelican 1040-cradle QI sides.stl
151.4 x 87.7 x 32.6
