Safecast/bGeigieZen/Misc documents  and software/3d models/plate for core1.FCStd

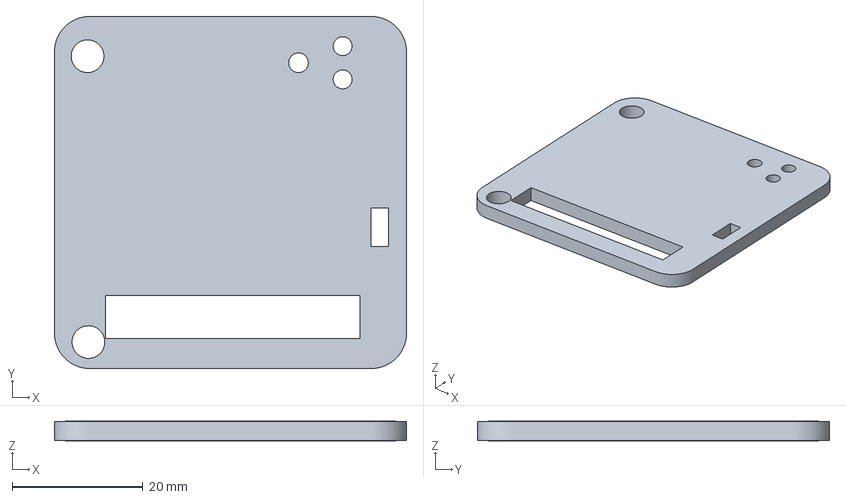
[picture p72: CAD file, 2024-09-23]
Misc documents and software/3d models/plate for core1.FCStd
53.8 x 53.8 x 3.00 mm
