Safecast/bGeigieZen/Misc documents  and software/3d models/Notecarrier-Mirco/Notecarrier-Micro/documentation/Notecarrier-B_Schematic_RevA.pdf

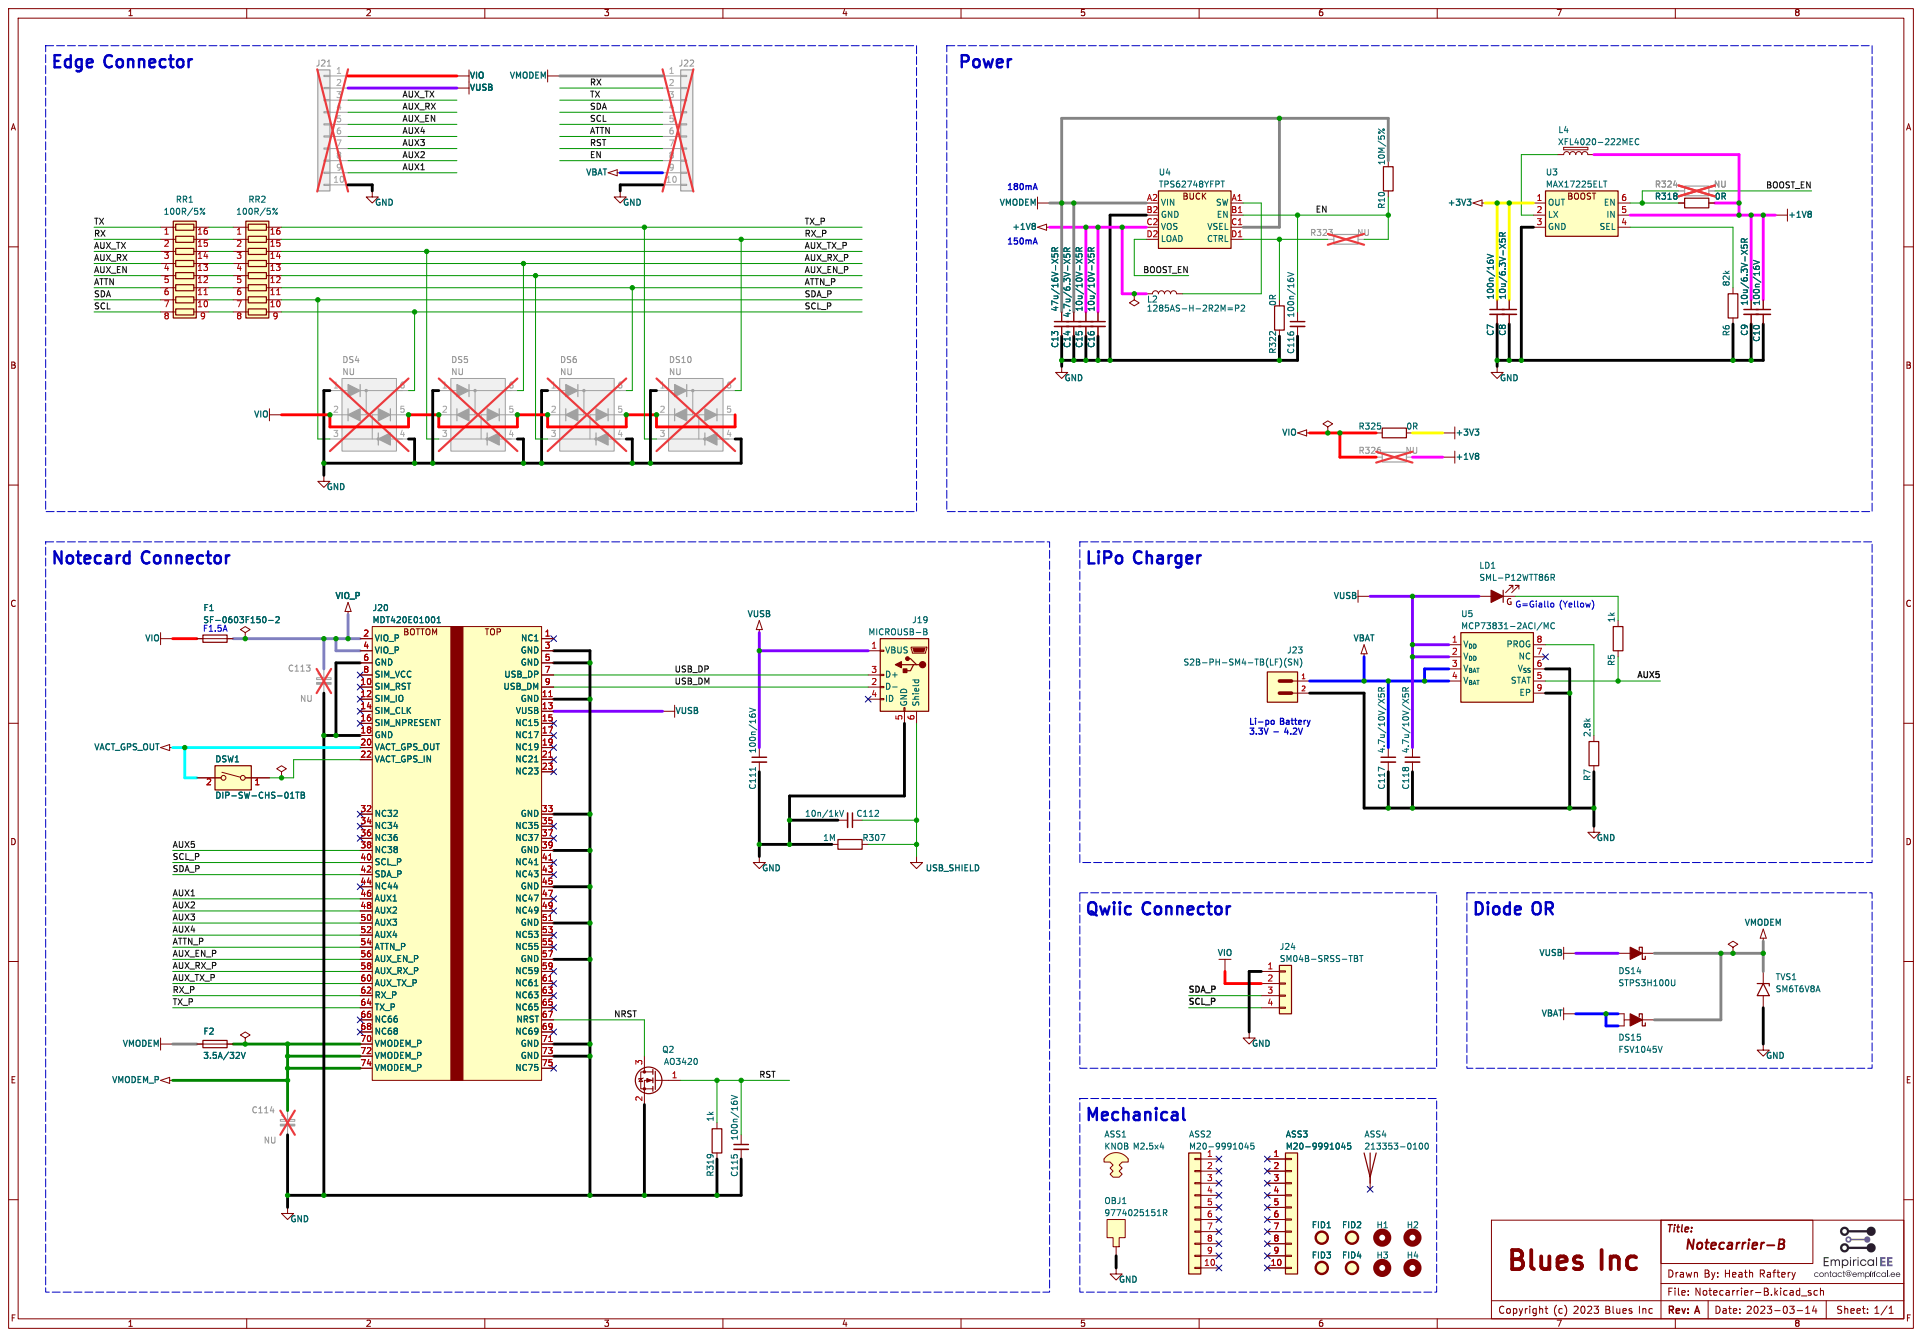
[picture p204: page 1]

2 3 Q2AO3420 GND C111 100n/16V GND C115 100n/16V R319 1k BOTTOM TOP NC1 1 SIM_RST 10 GND 11 SIM_IO 12 VUSB 13 SIM_CLK 14 NC15 15 SIM_NPRESENT 16 NC17 17 GND 18 NC19 19 VIO_P 2 VACT_GPS_OUT 20 NC21 21 VACT_GPS_IN 22 NC23 23 GND 3 NC32 32 GND 33 NC34 34 NC35 35 NC36 36 NC37 37 NC38 38 GND 39 VIO_P 4 SCL_P 40 NC41 41 SDA_P 42 NC43 43 NC44 44 GND 45 AUX1 46 NC47 47 AUX2 48 NC49 49 GND 5 AUX3 50 GND 51 AUX4 52 NC53 53 ATTN_P 54 NC55 55 AUX_EN_P 56 GND 57 AUX_RX_P 58 NC59 59 GND 6 AUX_TX_P 60 NC61 61 RX_P 62 NC63 63 TX_P 64 NC65 65 NC66 66 NRST 67 NC68 68 NC69 69 USB_DP 7 VMODEM_P 70 GND 71 VMODEM_P 72 GND 73 VMODEM_P 74 NC75 75 SIM_VCC 8 USB_DM 9
