Safecast/bGeigieZen/Misc documents  and software/Sch_Core2_v1.1_2024-02-22.pdf

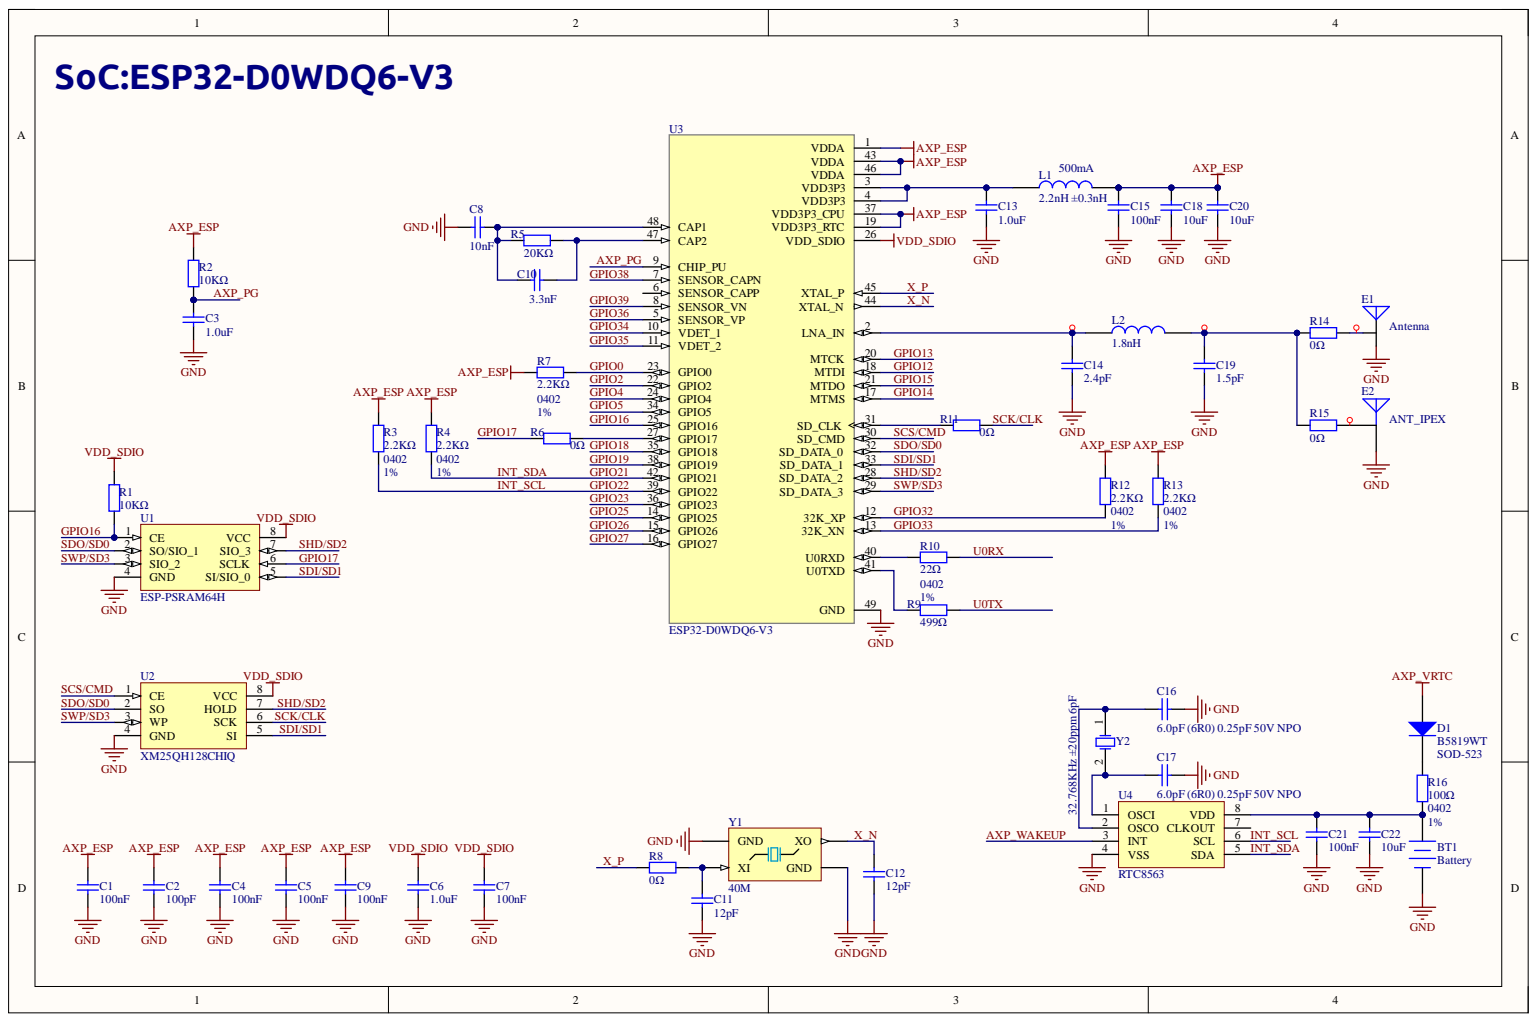
[picture p205: page 1]

CAP2 47

AXP_PG GPIO38 | CHIP_PU 9 SENSOR_CAPN 7

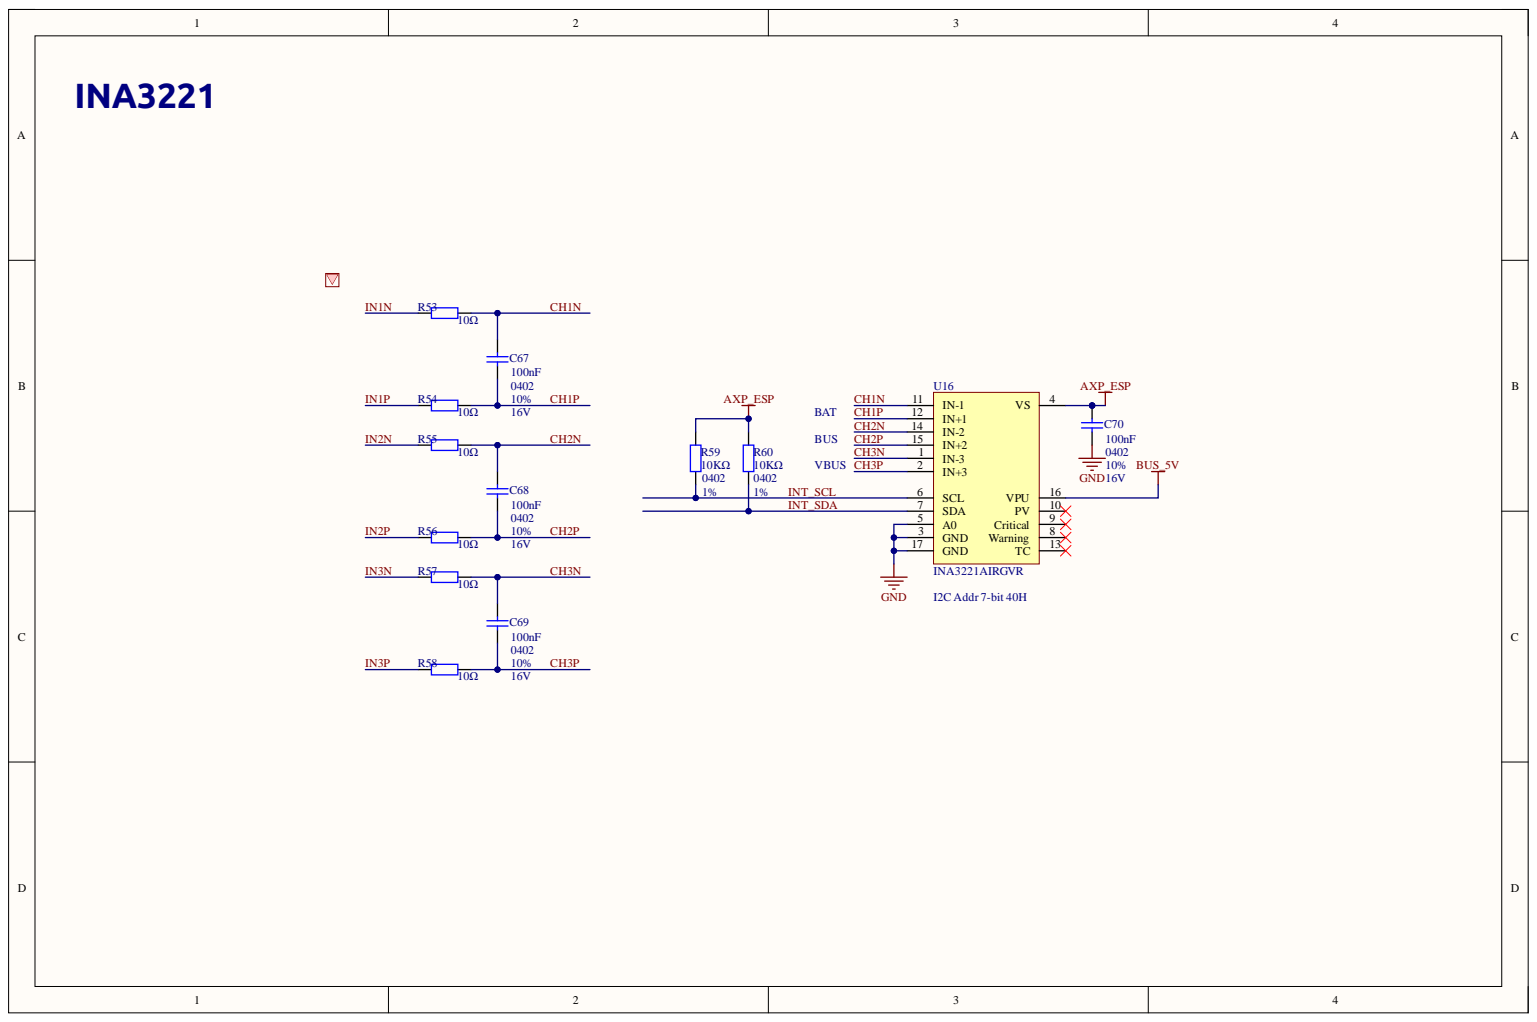
[picture p206: page 2]

1 7

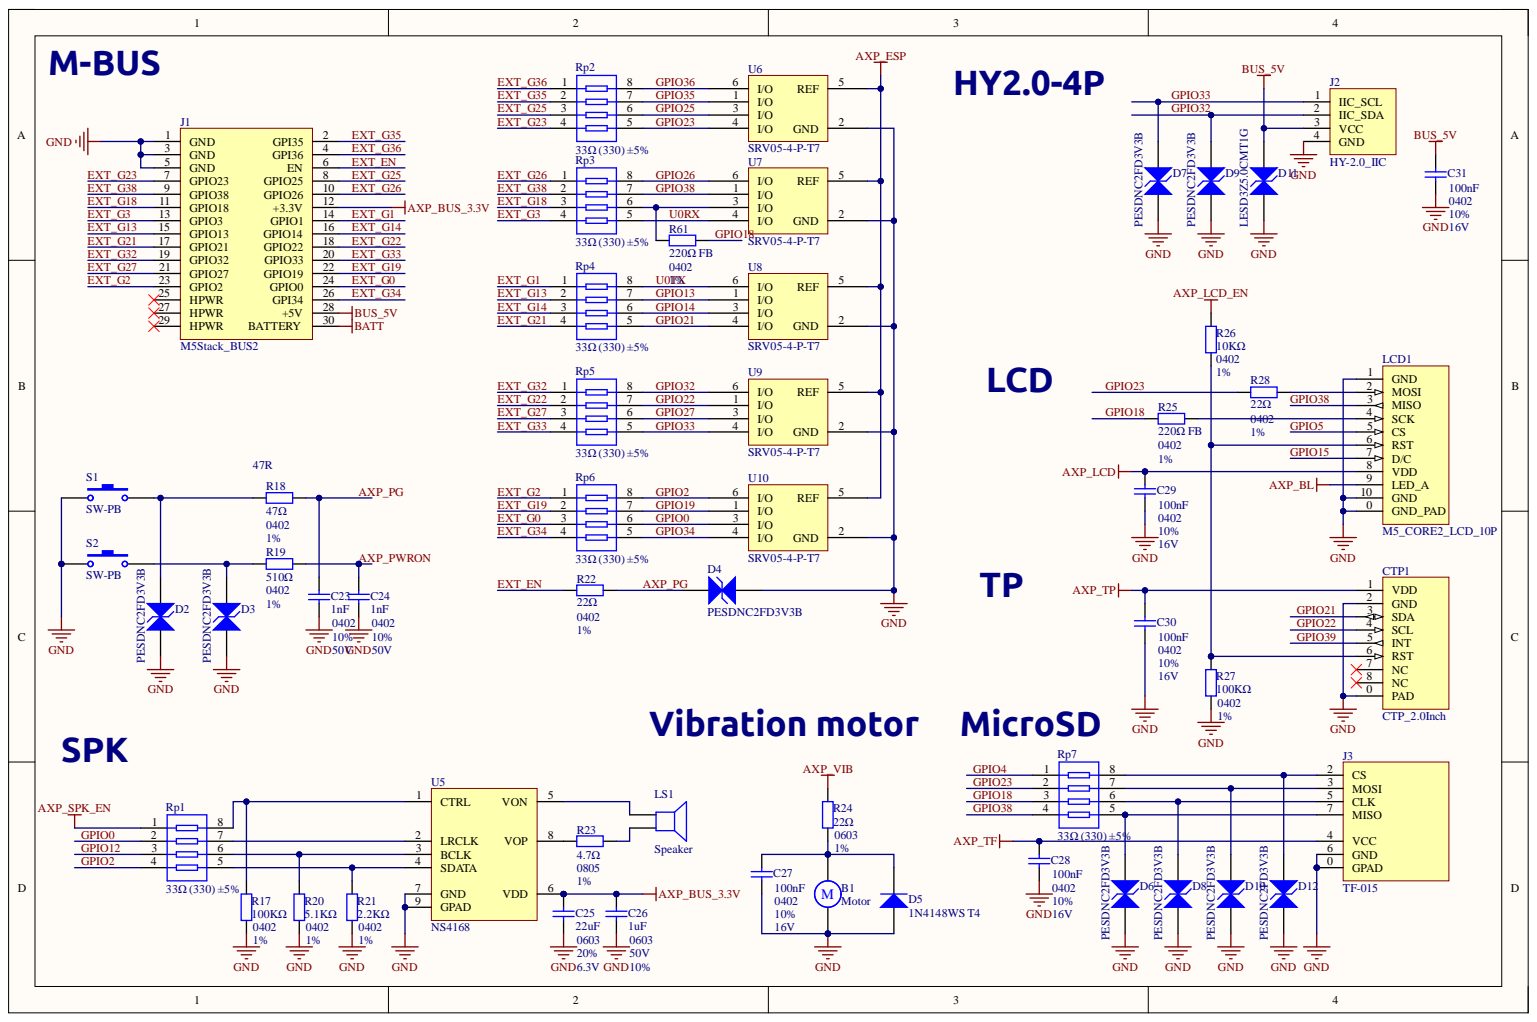
[picture p207: page 3]

3 4 5 6

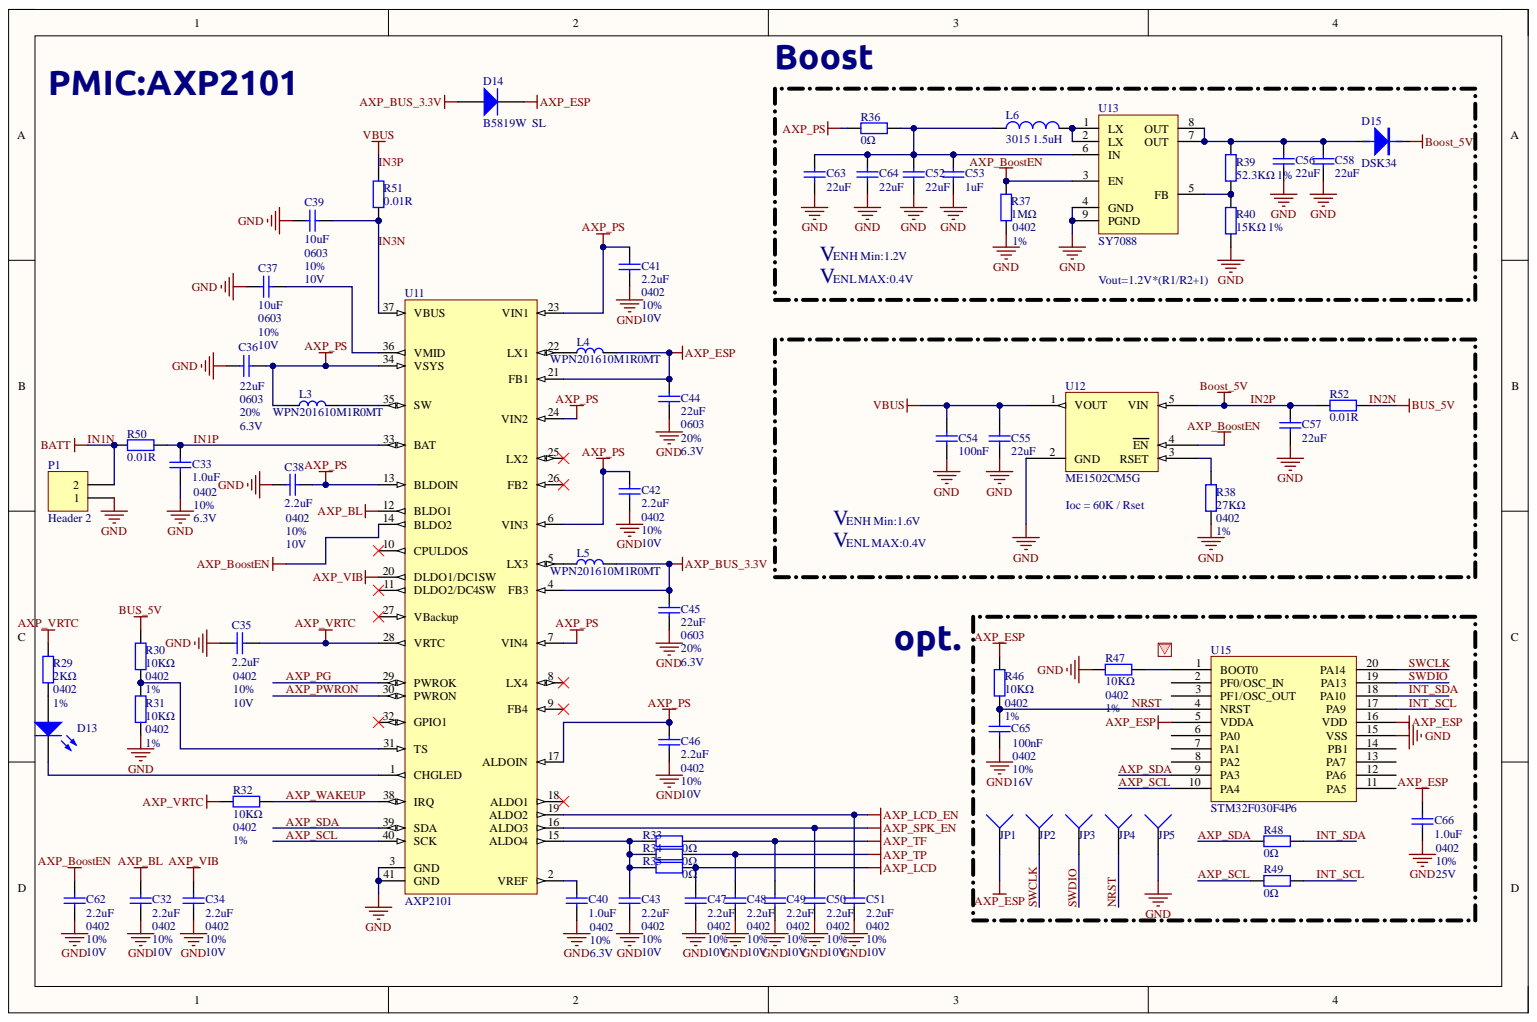
[picture p208: page 4]

10% 10V | CPULDOS 10

WPN201610M1R0MT

R34 | 0Ω
R35 | 0Ω

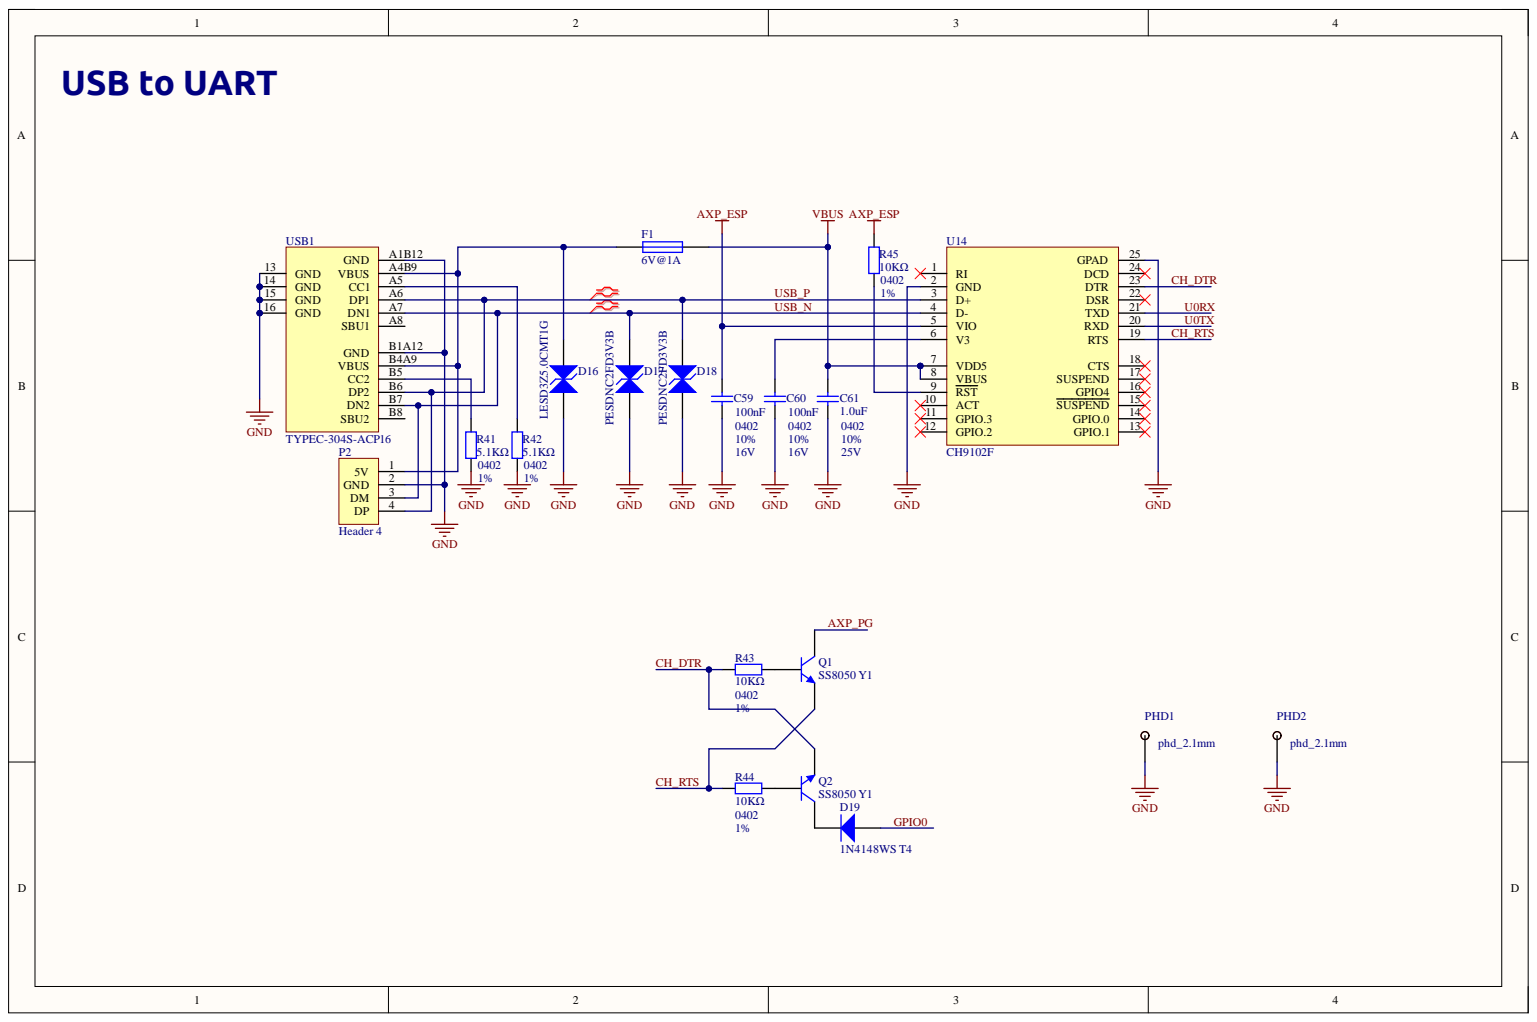
[picture p209: page 5]

1 6 | | A 7 | USB_ N | 4 | 15 GPIO4 16 SUSPEND 17 CTS 18 RTS 19 RXD 20 TXD 21 DSR 22 DTR 23 DCD 24 GPAD 25 4 SUSPEND

1 0
1 1 | | 1
1 2 | | 1 3
