Safecast/bGeigieZen/Misc documents  and software/Sch_Core2_v1.1_2023-07-20.pdf

CAP2 47

AXP_PG GPIO38 | CHIP_PU 9 SENSOR_CAPN 7

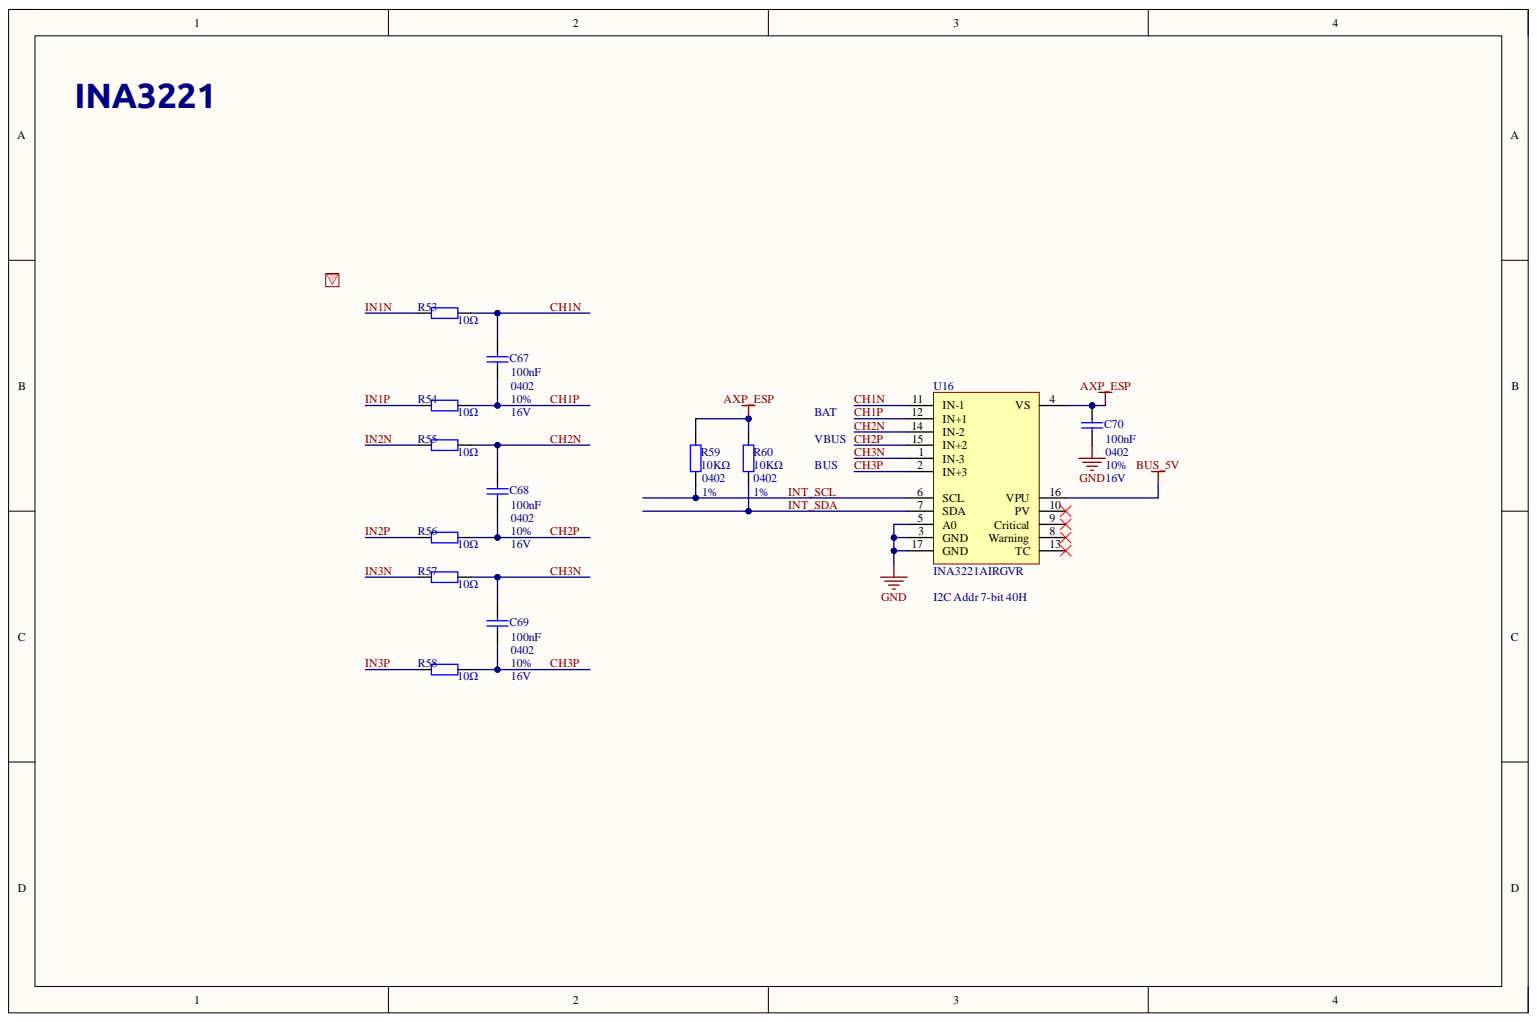
[picture p210: page 2]

1 7


3 4 5 6


10% 10V | CPULDOS 10

WPN201610M1R0MT

R34 | 0Ω
R35 | 0Ω

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

1 0
1 1 | | 1
1 2 | | 1 3
