Safecast/bGeigieZen/bgeigiezen_firmware/controller.h

#ifndef BGEIGIEZEN_CONTROLLER_H_
#define BGEIGIEZEN_CONTROLLER_H_

#include <Arduino.h>
#include <Aggregator.hpp>
#include <Handler.hpp>
#include <TeenyUbloxConnect.h>
#include "utils/sd_wrapper.h"
#include "workers/local_storage.h"

struct DeviceState {
  enum Mode {
    e_mode_not_set,
    e_mode_simple,
    e_mode_advanced,
  };

  bool initialized;
  bool local_available;
  SDInterface::SdStatus sd_card_status;
  Mode mode;

};


/**
 * Main controller for the system, implements state machine to run
 */
class Controller : public Aggregator, public Worker<DeviceState> {
 public:
  Controller(LocalStorage& settings, TeenyUbloxConnect& gnss);
  virtual ~Controller() = default;

  /**
   *
   */
  void initialize() override;

  /**
   * Starts default workers and handlers, loads SD
   */
  void start_default_workers();

  /**
   * Load SD config into device memory
   */
  bool load_sd_config();

  /**
   * Writes device settings onto SD
   *
   */
  bool write_sd_config();

  /**
   * Clears device memory, clears settings on the SD card, clears log files
   */
  bool factory_reset();

  /**
   * get GNSS instance
   */
  TeenyUbloxConnect& get_gnss();

  /**
   * Reset memory settings and restart system
   */
  void reset_settings();

  const LocalStorage& get_settings() const;

 private:
  /**
   * As a worker, the controller will notify of any state changes
   * @return
   */
  int8_t produce_data() override;

  bool _initialized;
  LocalStorage& _settings;
  TeenyUbloxConnect& _gnss;

};

#endif // BGEIGIEZEN_CONTROLLER_H_
