Safecast/bGeigieZen/bgeigie_firmware_pio/src/display.cpp

#include <M5Core2.h> // #include <M5Stack.h>

#include <cstdio>
#include <display.hpp>
#include <menu.hpp>

//setup brightness by Rob Oudendijk 2023-03-13
void core2Brightness(uint8_t lvl, bool overdrive = false) {
  // The backlight brightness is in steps of 25 in AXP192.cpp
  // calculation in SetDCVoltage: ( (voltage - 700) / 25 )
  // 2325 is the minimum "I can just about see a glow in a dark room" level of brightness.
  // 2800 is the value set by the AXP library as "standard" bright backlight.
  int v = lvl * 25 + 2300;

  // Clamp to safe values.
  if (v < 2300) v = 2300;
  if (overdrive) {
    if (v > 3200) v = 3200; // maximum of 3.2 volts, 3200 (uint8_t lvl  = 36) absolute max!
  } else {
    if (v > 2800) v = 2800; // maximum of 2.8 volts, 2800 (uint8_t lvl  = 20)
  }

  // Minimum brightness means turn off the LCD backlight.
  if (v == 2300) {
    // LED set to minimum brightness? Turn off.
    M5.Axp.SetDCDC3(false);
    return;
  } else {
    // Ensure backlight is on. (magic name = DCDC3)
    M5.Axp.SetDCDC3(true);
  }

  // Set the LCD backlight voltage. (magic number = 2)
  M5.Axp.SetDCVoltage(2, v);
}

// Menu state machine initialization
InitState mstate{};
InactiveState inactivestate{};
MenuContext mcontext{};


void Display::clear() {
  // Clear display
  M5.Lcd.clear();
  M5.lcd.setRotation(3);
  // prevent ghost buttons on logging and survey screens
  mcontext.button_dimblank.hide();
  mcontext.button_config_network.hide();
  M5.Lcd.setTextDatum(BL_DATUM);  // By default, text x,y is bottom left corner
  core2Brightness(LEVEL_BRIGHT);
  dimmingButton.setFont(1);
  //dimmingButton.setLabel("DIMMING");
  dimmingButton.draw();

  // Buttons defined in M5Core2.h
  // Hot zones start 40px above top of visible display
  // See discussion in M5Button.h and M5Touch.h
  M5.BtnA.set( 10, -40, 80, 70);
  M5.BtnB.set(120, -40, 80, 70);
  M5.BtnC.set(230, -40, 80, 70);
}

void Display::draw_base() {
  // Display safecast copyright
  M5.Lcd.setTextFont(1);
  M5.Lcd.setTextColor(TFT_WHITE, TFT_BLACK);
  M5.Lcd.drawString("SAFECAST", 230, 215, 1);
  M5.Lcd.setTextColor(TFT_ORANGE, TFT_BLACK);
  M5.Lcd.drawString("2023", 285, 215, 1);
}

void Display::draw_navbar(const char *A, const char *B, const char *C) {
  M5.Lcd.setTextColor(TFT_YELLOW, TFT_BLACK);
  // Reference the button coordinates
  draw_navbar_label(A, M5.BtnA); // Button A
  draw_navbar_label(B, M5.BtnB); // Button B
  draw_navbar_label(C, M5.BtnC); // Button C
}

void Display::draw_navbar_label(const char *s, const Button &b) {
  // Bottom-Centre of Button hot zone, font size 2
  auto previous_datum = M5.Lcd.getTextDatum();
  M5.Lcd.setTextDatum(BC_DATUM);
  M5.Lcd.drawString(s, b.x+(b.w/2), b.y+(b.h-10), 2);
  M5.Lcd.setTextDatum(previous_datum);
}

void Display::update() {
  // This function is mainly used to read the buttons and update the state
  // of the display

  bool button_A_pressed = M5.BtnA.wasPressed();
  bool button_B_pressed = M5.BtnB.wasPressed();
  bool button_C_pressed = M5.BtnC.wasPressed();
  bool background_pressed = M5.background.wasPressed();
  bool dimming_pressed = dimmingButton.wasPressed();
  bool anybutton_pressed = button_A_pressed
                           || button_B_pressed
                           || button_C_pressed
                           || background_pressed
                           || dimming_pressed;

  bool moved = mpu.motionDetected();

  if(dimming_pressed) {
    dimming_enabled = ! dimming_enabled;
    /* DEBUG */ Serial.print("Dimming button was pressed, dimming_enabled=");  Serial.println(dimming_enabled);
    if(dimming_enabled)
      dimmingButton.setLabel("DIMMING");
    else
      dimmingButton.setLabel("FIXED");
    }

  switch (state) {
    case (bGeigieZen::S_STARTUP):
      clear();  // initialize display
      draw_base();
      state = bGeigieZen::S_MAIN_DRAW;  // next state
      break;

    case (bGeigieZen::S_MAIN_DRAW):
      /*DEBUG*/ Serial.println("Entering bGeigieZen::S_MAIN_DRAW");
      /*DEBUG*/ Serial.printf("dimming_enabled = %s\n", dimming_enabled? "true":"false");
      timer_blanking.restart();
      timer_dimming.restart();
      clear();
      draw_base();
      state = bGeigieZen::S_MAIN_SHOW;
      break;

    case (bGeigieZen::S_MAIN_SHOW):
      draw_main();
      if (button_C_pressed) state = bGeigieZen::S_QRCODE_DRAW;
      if (button_B_pressed) state = bGeigieZen::S_SURVEY_DRAW;
      if (button_A_pressed) state = bGeigieZen::S_MENU_DRAW;
      if(anybutton_pressed || moved) {
        /*DEBUG*/ Serial.println("In bGeigieZen::S_MAIN_SHOW, restarting timers");
        core2Brightness(LEVEL_BRIGHT);
        timer_blanking.restart();
        timer_dimming.restart();
      }
      else if(dimming_enabled && timer_dimming.onExpired()) {
        /*DEBUG*/ Serial.println("In bGeigieZen::S_MAIN_SHOW, dimming");
        // dim the display
        core2Brightness(LEVEL_DIMMED);
      }
      else if(dimming_enabled && timer_blanking.onExpired()) {
        /*DEBUG*/ Serial.println("In bGeigieZen::S_MAIN_SHOW, blanking");
        // Turn off the display
        clear();
        core2Brightness(LEVEL_BLANKED);
        state = bGeigieZen::S_BLANKED;
      }
      break;

    case (bGeigieZen::S_QRCODE_DRAW):
      clear();
      draw_qrcode();
      state = bGeigieZen::S_QRCODE_SHOW;
      break;

    case (bGeigieZen::S_QRCODE_SHOW):
      if (anybutton_pressed)  // restore MAIN on any button pressed
        state = bGeigieZen::S_MAIN_DRAW;
      break;

    case (bGeigieZen::S_SURVEY_DRAW):
      clear();
      draw_base();
      state = bGeigieZen::S_SURVEY_SHOW;
      break;

    case (bGeigieZen::S_SURVEY_SHOW):
      draw_survey();
      if (button_C_pressed) state = bGeigieZen::S_QRCODE_DRAW;
      if (button_B_pressed) state = bGeigieZen::S_MAIN_DRAW;
      if (button_A_pressed) state = bGeigieZen::S_MENU_DRAW;
      if(anybutton_pressed || moved) {
        core2Brightness(LEVEL_BRIGHT);
        timer_blanking.restart();
        timer_dimming.restart();
      }
      else if(dimming_enabled && timer_dimming.onExpired()) {
        // dim the display
        core2Brightness(LEVEL_DIMMED);
      }
      else if(dimming_enabled && timer_blanking.onExpired()) {
        // Turn off the display
        clear();
        core2Brightness(LEVEL_BLANKED);
        state = bGeigieZen::S_SURVEY_BLANKED;
      }
      break;

    case (bGeigieZen::S_BLANKED):
      if(anybutton_pressed || moved) {
        core2Brightness(LEVEL_BRIGHT);
        state = bGeigieZen::S_MAIN_DRAW;
      }
      break;

    case (bGeigieZen::S_SURVEY_BLANKED):
      if(anybutton_pressed || moved) {
        core2Brightness(LEVEL_BRIGHT);
        state = bGeigieZen::S_SURVEY_DRAW;
      }
      break;

    case bGeigieZen::S_MENU_DRAW:
      /*DEBUG*/Serial.println("bGeigieZen::S_MENU_DRAW: calling mcontext.goto_state(&mstate)");
      /*DEBUG*/Serial.printf("&mstate = %04X\n", &mstate);
      mcontext.goto_state(&mstate, this);
      state = bGeigieZen::S_MENU_SHOW;
      break;
    /* case bGeigieZen::S_MENU_DRAW:
      clear();
      draw_base();
      draw_menu();
      state = bGeigieZen::S_MENU_SHOW;
      break; */

    case bGeigieZen::S_MENU_SHOW:
      if (button_B_pressed) {
        // When Return button pressed, set the menu state to "inactive",
        // erase and hide the buttons and return control to this FSM.
        mcontext.goto_state(&inactivestate, this);
        state = bGeigieZen::S_MAIN_DRAW;
        break;
      }
      mcontext.update();
      break;
  }
}

void Display::draw_qrcode() {
  // Create the QR code
  int w = (int)(0.9 * height);
  if (w % 2 == 1) w -= 1;
  int x = (width - w) / 2;
  int y = (height - w) / 2;

  // create the URL
  char url[sizeof(QR_CODE_URL_BASE) + QR_CODE_DEV_ID_NDIGITS];
  std::sprintf(url, "%s%04d", QR_CODE_URL_BASE, (int)data.device_id);

  dimmingButton.erase();
  M5.Lcd.qrcode(url, x, y, w, 3);
};

void Display::draw_main() {
  draw_navbar("MENU", "MODE", "QR");  // Buttons A, B, C

  showDeviceId(data.device_id);
  showBatteryLevel(data.battery_level);

// Text datum bottom left for all drawString() that follow
  M5.Lcd.setTextDatum(BL_DATUM);

  if (data.geiger_fresh) {
    if (data.geiger_valid)
      M5.Lcd.setTextColor(TFT_WHITE, TFT_BLACK);
    else
      M5.Lcd.setTextColor(TFT_YELLOW, TFT_BLACK);

    // Display CPM
    M5.Lcd.drawString("CPM ", 130, 90, 4);
    M5.Lcd.setCursor(120, 55);
    printIntFont(data.geiger_cpm, true, 5, 100, 5, 7);

    // Display uSv/h
    M5.Lcd.drawString("uSv/h =", 5, 140, 4);
    M5.Lcd.setCursor(100, 80);
    printFloatFont(data.geiger_uSv, true, 7, 3, 140, 140, 4);

    data.geiger_fresh = false;
  }

  // Display GPS data always, change colour if not fresh
  if (data.gps_fresh) {
    M5.Lcd.setTextColor(TFT_WHITE, BLACK);
    data.gps_fresh = false;
  }
  else {
    M5.Lcd.setTextColor(TFT_WHITE, TFT_BLACK);
  }
  M5.Lcd.setCursor(0, 150);
  M5.Lcd.print("Satelites  :");
  printInt(data.gps_satellites.value(), data.gps_satellites.isValid(), 5);
  M5.Lcd.println();
  M5.Lcd.print("Latitude   :");
  printFloat(data.gps_location.lat(), data.gps_location.isValid(), 11, 6);
  M5.Lcd.println();
  M5.Lcd.print("Longitude  :");
  printFloat(data.gps_location.lng(), data.gps_location.isValid(), 12, 6);
  M5.Lcd.println();
  M5.Lcd.print("Altitude   :");
  printFloat(data.gps_altitude.meters(), data.gps_altitude.isValid(), 7, 2);
  M5.Lcd.println();
  M5.Lcd.print("Heading    :");
  printFloat(data.gps_course.deg(), data.gps_course.isValid(), 7, 2);
  M5.Lcd.println();
  M5.Lcd.print("Speed      :");
  printFloat(data.gps_speed.kmph(), data.gps_speed.isValid(), 6, 2);
  M5.Lcd.println();
  M5.Lcd.print("Date       :");
  printDate(data.gps_date);
  M5.Lcd.println();
  M5.Lcd.print("Time       :");
  printTime(data.gps_time);
}

void Display::draw_survey() {

  draw_navbar("MENU", "MODE", "QR");  // Buttons A, B, C

  showDeviceId(data.device_id);
  showBatteryLevel(data.battery_level);

// Text datum bottom left for all drawString() that follow
  M5.Lcd.setTextDatum(BL_DATUM);

  if (data.geiger_fresh) {
    if (data.geiger_valid)
      M5.Lcd.setTextColor(TFT_WHITE, TFT_BLACK);
    else
      M5.Lcd.setTextColor(TFT_YELLOW, TFT_BLACK);

    // Display uSv/h
    M5.Lcd.drawString("uSv/h", 200, 100, 4);
    printFloatFont(data.geiger_uSv, true, 7, 3, 100, 5, 7);

    // Display CPM
    M5.Lcd.drawString("CPM", 75, 135, 4);
    printIntFont(data.geiger_cpm, true, 5, 135, 5, 4);

    // Display Bq/m^2
    M5.Lcd.drawString("Bq/m^2", 75, 160, 4);
     printFloatFont(data.geiger_bqm2, true, 5, 3, 160, 5, 4);

    // Display Max. uSv/h
    M5.Lcd.drawString("Max", 180, 125, 2);
    printFloatFont(/*data.geiger_uSv*/0.1234, true, 7, 3, 125, 220, 2);
    M5.Lcd.drawString("uSv/h", 270, 125, 2);

    // Display dose in uSv
    M5.Lcd.drawString("Dose", 180, 140, 2);
    printFloatFont(/*data.geiger_uSv*/12.345, true, 7, 3, 140, 220, 2);
    M5.Lcd.drawString("uSv", 270, 140, 2);

    data.geiger_fresh = false;
  }

  // Display reduced set of GPS data, change colour if not fresh
  if (data.gps_fresh) {
    M5.Lcd.setTextColor(TFT_WHITE, BLACK);
    data.gps_fresh = false;
  }
  else {
    M5.Lcd.setTextColor(TFT_YELLOW, TFT_BLACK);
  }
  M5.Lcd.setCursor(0, 165);
  M5.Lcd.print("Satelites  :");
  printInt(data.gps_satellites.value(), data.gps_satellites.isValid(), 5);
  M5.Lcd.println();
  M5.Lcd.print("Latitude   :");
  printFloat(data.gps_location.lat(), data.gps_location.isValid(), 11, 6);
  M5.Lcd.println();
  M5.Lcd.print("Longitude  :");
  printFloat(data.gps_location.lng(), data.gps_location.isValid(), 12, 6);
  M5.Lcd.println();
  M5.Lcd.print("Altitude   :");
  printFloat(data.gps_altitude.meters(), data.gps_altitude.isValid(), 7, 2);
  M5.Lcd.println();
  M5.Lcd.print("Date       :");
  printDate(data.gps_date);
  M5.Lcd.println();
  M5.Lcd.print("Time       :");
  printTime(data.gps_time);
}

void Display::draw_menu() {
  draw_navbar("MENU", "MODE", "QR");  // Buttons A, B, C

  showDeviceId(data.device_id);
  showBatteryLevel(data.battery_level);

// Text datum bottom left for all drawString() that follow
  M5.Lcd.setTextDatum(BL_DATUM);
  // Display something
  M5.Lcd.drawString("MENU ITEM", 100, 40, 4);
  Button enable_ap_button{100, 40, 60, 50, false, "Enable AP", {TFT_YELLOW, TFT_DARKGREY, TFT_GREEN}};
  enable_ap_button.draw();
}

void Display::feed(const GeigerCounter &geiger_count) {
  data.geiger_valid = geiger_count.valid();
  data.geiger_cpm = geiger_count.per_minute();
  data.geiger_uSv = geiger_count.uSv();
  data.geiger_fresh = true;
}

void Display::feed(GPSSensor &gps) {
  // Here we can't make the ref const because we need to access the fields
  // of the TinyGPS object directly...

  data.gps_satellites = gps.data().satellites;
  data.gps_speed = gps.data().speed;
  data.gps_course = gps.data().course;
  data.gps_location = gps.data().location;
  data.gps_altitude = gps.data().altitude;
  data.gps_time = gps.data().time;
  data.gps_date = gps.data().date;
  data.gps_fresh = true;
}

void Display::showDeviceId(uint32_t id, int16_t x, int16_t y) {
  // Show the device number
  M5.Lcd.setCursor(x, y);
  M5.Lcd.setTextFont(1);
  M5.Lcd.setTextColor(TFT_ORANGE, TFT_BLACK);
  M5.Lcd.print("DeviceID ");
  M5.Lcd.print(id);
}

void Display::showBatteryLevel(float level, int16_t x, int16_t y) {
  // Display battery level
  M5.Lcd.setCursor(x, y);  // (270, 30);
  M5.Lcd.setTextFont(1);
  M5.Lcd.setTextColor(TFT_ORANGE, TFT_BLACK);
  if (level < 0.0) {
    M5.Lcd.print("BAT=ext");
  }
  else {
    M5.Lcd.print("BAT=");
    M5.Lcd.print(level, 0);
    M5.Lcd.print("%");
  }
}

void printFloat(float val, bool valid, int len, int prec) {
  if (!valid) {
    while (len-- > 1) M5.Lcd.print('*');
    M5.Lcd.print(' ');
  } else {
    M5.Lcd.print(val, prec);
    int vi = abs((int)val);
    int flen = prec + (val < 0.0 ? 2 : 1);  // . and -
    flen += vi >= 1000 ? 4 : vi >= 100 ? 3 : vi >= 10 ? 2 : 1;
    for (int i = flen; i < len; ++i) M5.Lcd.print(' ');
  }
  delay(0);
}

void printFloatFont(float val, bool valid, int len, int prec, int y, int x,
                    int font) {
  if (!valid) {
    while (len-- > 1) M5.Lcd.print('*');
    M5.Lcd.print(' ');
  } else {
    char sz[32] = "*****************";
    if (valid) sprintf(sz, "%f", val);
    sz[len] = 0;
    for (int i = strlen(sz); i < len; ++i) sz[i] = ' ';
    if (len > 0) sz[len - 1] = ' ';
    M5.Lcd.drawString((sz), x, y, font);

    int vi = abs((int)val);
    int flen = prec + (val < 0.0 ? 2 : 1);  // . and -
    flen += vi >= 1000 ? 4 : vi >= 100 ? 3 : vi >= 10 ? 2 : 1;
    for (int i = flen; i < len; ++i) M5.Lcd.drawString("", x, y, font);
  }
  delay(0);
}

// Prints int
void printInt(unsigned long val, bool valid, int len) {
  char sz[32] = "*****************";
  if (valid) sprintf(sz, "%ld", val);
  sz[len] = 0;
  for (int i = strlen(sz); i < len; ++i) sz[i] = ' ';
  if (len > 0) sz[len - 1] = ' ';
  M5.Lcd.print(sz);
  delay(0);
}

// Prints int with fonts
void printIntFont(unsigned long val, bool valid, int len, int y, int x,
                  int font) {
  char sz[32] = "*****************";
  if (valid) sprintf(sz, "%ld", val);
  sz[len] = 0;
  for (int i = strlen(sz); i < len; ++i) sz[i] = ' ';
  if (len > 0) sz[len - 1] = ' ';
  M5.Lcd.drawString((sz), x, y, font);
  delay(0);
}

// Prints date
void printDate(TinyGPSDate &d) {
  if (!d.isValid()) {
    M5.Lcd.print(F("********** "));
  } else {
    char sz[32];
    sprintf(sz, "%02d/%02d/%02d ", d.year(), d.month(), d.day());
    M5.Lcd.print(sz);
  }
  printInt(d.age(), d.isValid(), 5);  // age in milliseconds
  delay(0);
}

// Prints time
void printTime(TinyGPSTime &t) {
  if (!t.isValid()) {
    M5.Lcd.print(F("******** "));
  } else {
    char sz[32];
    sprintf(sz, "%02d:%02d:%02d ", t.hour(), t.minute(), t.second());
    M5.Lcd.print(sz);
  }
  delay(0);
}

  // Misc set/get
  void Display::set_dimblank_delays(uint32_t dimdelay, uint32_t blankdelay) {
    /*DEBUG*/ Serial.printf("Display::set_dimblank_delays(%d, %d)\n", dimdelay, blankdelay);
    if((0 == dimdelay) || (0 == blankdelay)) { 
      dimming_enabled = false;
      dimmingButton.setLabel("FIXED");
    }
    else {
      timer_dimming.setTimeout(dimdelay);
      timer_blanking.setTimeout(blankdelay);
      timer_dimming.restart();
      timer_blanking.restart();
      dimming_enabled = true;
      dimmingButton.setLabel("DIMMING");
    }
  }
