Safecast/bGeigieZen/bgeigiezen_firmware/workers/navsat_collector.h

#ifndef BGEIGIEZEN_NAVSAT_COLLECTOR_H_
#define BGEIGIEZEN_NAVSAT_COLLECTOR_H_

#include <Worker.hpp>
#include <TeenyUbloxConnect.h>
#include "gps_connector.h"


struct NavsatData {
  bool available;
  ubloxNAVSATInfo_t navsat_info;

};

/**
 * GPS device worker, produces the current GPS location.
 */
class NavsatCollector : public Worker<NavsatData> {
 public:

  explicit NavsatCollector(TeenyUbloxConnect& _gnss, GpsConnector& gps);

  virtual ~NavsatCollector() = default;

  bool activate(bool retry) override;

  void deactivate() override;

  int8_t produce_data() override;

 private:
  TeenyUbloxConnect& _gnss;
  GpsConnector& _gps;
  const GnssData& _gps_data;
  uint32_t _last_gsv_cycle;
};

#endif //BGEIGIEZEN_NAVSAT_COLLECTOR_H_
