Safecast/bGeigieZen/bgeigie_firmware_pio/include/wifi_connection.hpp

#ifndef BGEIGIEZEN_WIFI_CONNECTION_H_
#define BGEIGIEZEN_WIFI_CONNECTION_H_

class WiFiConnection {

 public:
  // WiFi parameters
  char myWifiSSID [32] = {'\0'};
  char myIPaddr[16] = {'\0'};
  char configWifiSSID [32] = {'\0'};
  char configWifiPreSharedKey [32] = {'\0'};
  char configIPaddr [20] = {'\0'};

  /**
   * Connect to wifi endpoint
   * @param ssid
   * @param password
   * @return true if connected
   */
  static bool connect_wifi(const char* ssid, const char* password = nullptr);

  /**
   * disconnect from wifi endpoint
   */
  static void disconnect_wifi();

  /**
   * check if wifi is connected
   * @return
   */
  static bool wifi_connected();

  /**
   * Start access point server
   * @return true if up
   */
  static bool start_ap_server(const char* host_ssid, const char* password);

  /**
   * Stop access point server
   */
  static void stop_ap_server();

  /**
   * check if wifi is connected
   * @return
   */
  static bool ap_server_up();

  /**
   * Set wifi hostname
   */
  static void set_hostname(const char* hostname);
};


#endif //BGEIGIEZEN_WIFI_CONNECTION_H_
