Safecast/bGeigieZen/bgeigie_firmware_pio/test/OR code.ino

#include <M5Core2.h> // #include <M5Stack.h>

void setup() {
  M5.begin();
  M5.Power.begin();
  // Display QRCode
  M5.Lcd.qrcode("https://grafana.safecast.cc/d/DFSxrOLWk/safecast-device-details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");
  // M5.Lcd.qrcode(const char *string, uint16_t x = 50, uint16_t y = 10, uint8_t width = 220, uint8_t version = 6);
}

void loop() {
}
