Safecast/bGeigieZen/bgeigiezen_firmware/utils/http_pages.cpp

#include "http_pages.h"
#include "user_config.h"

#define TITLE_HOME "Home"
#define TITLE_CONF_DEVICE "Configure device"
#define TITLE_CONF_LOCATION "Configure location"
#define TITLE_CONF_CONNECTION "Configure connection"

const char* success_message = "<p><em>Configurations saved!</em></p>";

const char* local_resources =
    "<link rel='stylesheet' href='/pure.css'>";

const char* online_resources =
    "<script src='https://ajax.googleapis.com/ajax/libs/jquery/3.2.1/jquery.min.js'></script>"
    "<link rel='stylesheet' href='https://use.fontawesome.com/releases/v5.8.2/css/all.css' "
    "integrity='sha384-oS3vJWv+0UjzBfQzYUhtDYW+Pj2yciDJxpsK1OYPAYjqT085Qq/1cq5FLXAZQ7Ay' crossorigin='anonymous'>";

const char* fallback_resources =
    "";

/**
 * page format
 * %s - page name (page title)
 * %d - device id (page title)
 * %s - remote resources
 * %s - local resources
 * %d - device id (menu title)
 * %s - page content (main content)
 */
const char* base_page_format_begin =
    "<!DOCTYPE html>"
    "<html lang='en'><head>"
    "<meta name='viewport' content='width=device-width, initial-scale=1.0'>"
    "<title>%s | bGeigieZen %d</title>"
    "%s"
    "%s"
    "<style>"
    "i{width: 25px;text-align: center;}"
    "#layout{max-width: 680px;margin: auto;}"
    "#main{padding:1em;}"
    "input[type='text'],input[type='number']{max-width: 300px;width: 100%%;}"
    ".pure-menu-link{padding: 1em .7em;}"
    "</style>"
    "</head>"
    "<body>"
    "<div id='layout'>"
    "<div id='header'>"
    "<div class='pure-menu pure-menu-horizontal'>"
    "<a href='/' class='pure-menu-heading'>bGeigieZen %d</a>"
    "<ul class='pure-menu-list'>"
    "<li class='pure-menu-item'><a href='/device' class='pure-menu-link'><i class='fa fa-tablet'></i>Device</a></li>"
    "<li class='pure-menu-item'><a href='/connection' class='pure-menu-link'><i class='fa fa-wifi'></i>Connection</a></li>"
    "<li class='pure-menu-item'><a href='/location' class='pure-menu-link'><i class='fa fa-map-marker-alt'></i>Location</a></li>"
    "<li class='pure-menu-item'><a target='_blank' href='https://github.com/Safecast/bGeigieZen/' class='pure-menu-link'><i class='fab fa-github'></i>Github</a></li>"
    "</ul>"
    "</div>"
    "</div>"
    "<script>"
    "document.querySelectorAll('.pure-menu-item').forEach((e)=>e.children[0].href===window.location.href?e.classList.add('pure-menu-selected'):0);"
    "</script>"
    "<div id='main'>";

const char* base_page_format_end =
    "</div>"
    "</div>"
    "</body></html>";

const char* HttpPages::get_home_page(const LocalStorage& settings) {

  char grafana_url[130];
  sprintf(grafana_url, FIXED_MODE_GRAFANA_URL, settings.get_fixed_device_id(), settings.get_fixed_device_id());

  return render_full_page(
      settings.get_device_id(),
      TITLE_HOME,
      "<h1>Manage your bGeigieZen</h1>"
      "<p class='pure-form-message'>bGeigieZen version %s</p>"
      "<p>"
      "<ul>"
      "<li><a href='/device'>Configure device settings</a></li>"
      "<li><a href='/connection'>Configure Network connections</a></li>"
      "<li><a href='/location'>Configure location settings for Real Time mode</a></li>"
      "</ul>"
      "More information about configurations in the <a href='https://github.com/Safecast/bGeigieZen/wiki/User-manual#available-settings' target='_blank'>User manual</a>. "
      "Or view your device on <a href='%s' target='_blank'>Grafana</a>."
      "</p>",
      VERSION_NUMBER,
      grafana_url
  );
}

const char* HttpPages::get_config_device_page(
    bool display_success,
    const LocalStorage& settings
) {
  return render_full_page(
      settings.get_device_id(),
      TITLE_CONF_DEVICE,
      "<form class='pure-form pure-form-stacked' action='/save?next=/device' method='POST'>"
      "<fieldset>"
      "<legend><a href='/'>Home</a> / Device settings</legend>"

      // Alarm threshold
      "<label for='" FORM_NAME_ALERT_THRESHOLD "'>CPM Alert threshold</label>"
      "<input required type='number' min='0' max='34464' name='" FORM_NAME_ALERT_THRESHOLD "' id='" FORM_NAME_ALERT_THRESHOLD "' value='%u' step='1'>"
      "<span class='pure-form-message'>When in Real Time mode and CPM is above configured value, it will upload data more frequently</span>"

      // Screen dim timeout
      "<label for='" FORM_NAME_SCREEN_DIM_TIMEOUT "'>Screen dims after... (in seconds)</label>"
      "<input required type='number' min='0' max='34464' name='" FORM_NAME_SCREEN_DIM_TIMEOUT "' id='" FORM_NAME_SCREEN_DIM_TIMEOUT "' value='%u' step='1'>"
      "<span class='pure-form-message'>Set to 0 to disable screen dimming</span>"

      // Screen off timeout
      "<label for='" FORM_NAME_SCREEN_OFF_TIMEOUT "'>Screen turns off after... (in seconds)</label>"
      "<input required type='number' min='0' max='34464' name='" FORM_NAME_SCREEN_OFF_TIMEOUT "' id='" FORM_NAME_SCREEN_OFF_TIMEOUT "' value='%u' step='1'>"
      "<span class='pure-form-message'>Set to 0 to disable turning the screen turning off</span>"

      // Animated screensaver
      "<label>Screen when off</label>"
      "<label for='" FORM_NAME_ANIMATED_SCREENSAVER "0' class='pure-radio'>"
      "<input id='" FORM_NAME_ANIMATED_SCREENSAVER "0' type='radio' name='" FORM_NAME_ANIMATED_SCREENSAVER "' value='0' %s>Screen is completely off"
      "</label>"
      "<label for='" FORM_NAME_ANIMATED_SCREENSAVER "1' class='pure-radio'>"
      "<input id='" FORM_NAME_ANIMATED_SCREENSAVER "1' type='radio' name='" FORM_NAME_ANIMATED_SCREENSAVER "' value='1' %s>Animated screensaver"
      "</label>"
      "<br>"

      // Screen unit
      "<label>Big radiation value on display</label>"
      "<label for='" FORM_NAME_CPM_USVH "0' class='pure-radio'>"
      "<input id='" FORM_NAME_CPM_USVH "0' type='radio' name='" FORM_NAME_CPM_USVH "' value='0' %s>Value in uSv/h (micro Sievert per hour)"
      "</label>"
      "<label for='" FORM_NAME_CPM_USVH "1' class='pure-radio'>"
      "<input id='" FORM_NAME_CPM_USVH "1' type='radio' name='" FORM_NAME_CPM_USVH "' value='1' %s>Value in CPM (Clicks Per Minute)"
      "</label>"
      "<br>"

      // Manual logging
      "<h3>Logging options</h3>"
      "<label for='" FORM_NAME_MANUAL_LOGGING "0' class='pure-radio'>"
      "<input id='" FORM_NAME_MANUAL_LOGGING "0' type='radio' name='" FORM_NAME_MANUAL_LOGGING "' value='0' %s>Start logging when entering screen"
      "</label>"
      "<label for='" FORM_NAME_MANUAL_LOGGING "1' class='pure-radio'>"
      "<input id='" FORM_NAME_MANUAL_LOGGING "1' type='radio' name='" FORM_NAME_MANUAL_LOGGING "' value='1' %s>Manually start logging (button)"
      "</label>"
      "<span class='pure-form-message'>This is for drive and survey mode</span>"

      "<br>"

      // Journal logging
      "<label for='" FORM_NAME_ENABLE_JOURNAL "1' class='pure-radio'>"
      "<input id='" FORM_NAME_ENABLE_JOURNAL "1' type='radio' name='" FORM_NAME_ENABLE_JOURNAL "' value='1' %s>Create journal logs"
      "</label>"
      "<label for='" FORM_NAME_ENABLE_JOURNAL "0' class='pure-radio'>"
      "<input id='" FORM_NAME_ENABLE_JOURNAL "0' type='radio' name='" FORM_NAME_ENABLE_JOURNAL "' value='0' %s>Don't create journal logs"
      "</label>"
      "<span class='pure-form-message'>The journal log will contain all data lines regardless of which screen you're on</span>"

      "<br>"

      "<br>"
      "<button type='submit' class='pure-button pure-button-primary'>Save</button>"
      "</fieldset>"
      "</form>"
      "%s", // Success message
      settings.get_alert_threshold(),
      settings.get_screen_dim_timeout(),
      settings.get_screen_off_timeout(),
      settings.get_animated_screensaver() ? "" : "checked",
      settings.get_animated_screensaver() ? "checked" : "",
      settings.get_cpm_usvh() ? "" : "checked",
      settings.get_cpm_usvh() ? "checked" : "",
      settings.get_manual_logging() ? "" : "checked",
      settings.get_manual_logging() ? "checked" : "",
      settings.get_enable_journal() ? "checked" : "",
      settings.get_enable_journal() ? "" : "checked",
      display_success ? success_message : ""
  );
}

const char* HttpPages::get_config_location_page(
    bool display_success,
    const LocalStorage& settings
) {
  return render_full_page(
      settings.get_device_id(),
      TITLE_CONF_LOCATION,
      "<form class='pure-form pure-form-stacked' action='/save?next=/location' method='POST'>"
      "<fieldset>"
      "<legend><a href='/'>Home</a> / Location settings</legend>"


      // Home latitude
      "<label for='" FORM_NAME_LOC_FIXED_LAT "'>Real Time latitude</label>"
      "<input type='number' min='-90.0000' max='90.0000' name='" FORM_NAME_LOC_FIXED_LAT "' id='" FORM_NAME_LOC_FIXED_LAT "' value='%.5f' step='0.00001'>"

      // Home longitude
      "<label for='" FORM_NAME_LOC_FIXED_LON "'>Real Time longitude</label>"
      "<input type='number' min='-180.0000' max='180.0000' name='" FORM_NAME_LOC_FIXED_LON "' id='" FORM_NAME_LOC_FIXED_LON "' value='%.5f' step='0.00001'>"

      // Set last known location
      "<span class='pure-form-message'>"
      "Last known location (<a href='#' onclick=\""
      "document.getElementById('" FORM_NAME_LOC_FIXED_LAT "').value = document.getElementById('l_la').innerHTML;"
      "document.getElementById('" FORM_NAME_LOC_FIXED_LON "').value = document.getElementById('l_lo').innerHTML;"
      "return false;"
      "\">apply</a>):<br>"
      "Latitude: <span id='l_la'>%.5f</span><br>"
      "Longitude: <span id='l_lo'>%.5f</span><br>"
      "</span>"

      // Fixed range
      "<label for='" FORM_NAME_FIXED_RANGE "'>Real Time range</label>"
      "<input type='number' min='0' max='5' name='" FORM_NAME_FIXED_RANGE "' id='" FORM_NAME_FIXED_RANGE "' value='%.1f' step='0.1'>"
      "<span class='pure-form-message'>Range from Real Time location in which measurements will be posted as Real Time location (in KM)</span>"

      // Max DOP
      "<label for='" FORM_NAME_DOP_MAX "'>DOP max</label>"
      "<input type='number' min='100' max='5000' name='" FORM_NAME_DOP_MAX "' id='" FORM_NAME_DOP_MAX "' value='%u' step='1'>"
      "<span class='pure-form-message'>Max accepted DOP value for fix to be valid. Above value is configured as *100 (so a value of 500 would mean DOP of 5)</span>"


      "<br>"
      "<button type='submit' class='pure-button pure-button-primary'>Save</button>"
      "</fieldset>"
      "</form>"
      "%s", // Success message
      settings.get_fixed_latitude(),
      settings.get_fixed_longitude(),
      settings.get_last_latitude(),
      settings.get_last_longitude(),
      settings.get_fixed_range(),
      settings.get_dop_max(),
      display_success ? success_message : ""
  );
}

const char* HttpPages::get_config_connection_page(
    bool display_success,
    const LocalStorage& settings
) {
  char ssid[20];
  sprintf(ssid, ACCESS_POINT_SSID, settings.get_device_id());
  return render_full_page(
      settings.get_device_id(),
      TITLE_CONF_CONNECTION,
      "<form class='pure-form pure-form-stacked' action='/save?next=/connection' method='POST'>"
      "<fieldset>"
      "<legend><a href='/'>Home</a> / Connection settings</legend>"

      // Zen direct access point password
      "<label for='" FORM_NAME_AP_LOGIN "'>bGeigieZen password</label>"
      "<input type='text' name='" FORM_NAME_AP_LOGIN "' id='" FORM_NAME_AP_LOGIN "' value='%s' required>"
      "<span class='pure-form-message'>"
      "The password for the wifi access point when starting the bGeigieZen configuration server. "
      "The network name of your bGeigieZen will be: bgeigiezen-%d"
      "</span>"

      // WiFi ssid
      "<label for='" FORM_NAME_WIFI_SSID "'>WiFi network name</label>"
      "<input type='text' name='" FORM_NAME_WIFI_SSID "' id='" FORM_NAME_WIFI_SSID "' value='%s'>"
      "<span class='pure-form-message'>Your local WiFi network name</span>"

      // WiFi password (Profile 1)
      "<label for='" FORM_NAME_WIFI_PASS "'>WiFi password</label>"
      "<input type='text' name='" FORM_NAME_WIFI_PASS "' id='" FORM_NAME_WIFI_PASS "' value='%s'>"
      "<span class='pure-form-message'>Your local WiFi network password</span>"

      // WiFi ssid (Profile 2)
      "<label for='" FORM_NAME_WIFI_SSID2 "'>WiFi network name (Profile 2)</label>"
      "<input type='text' name='" FORM_NAME_WIFI_SSID2 "' id='" FORM_NAME_WIFI_SSID2 "' value='%s'>"
      "<span class='pure-form-message'>Optional second WiFi network name</span>"

      // WiFi password (Profile 2)
      "<label for='" FORM_NAME_WIFI_PASS2 "'>WiFi password (Profile 2)</label>"
      "<input type='text' name='" FORM_NAME_WIFI_PASS2 "' id='" FORM_NAME_WIFI_PASS2 "' value='%s'>"
      "<span class='pure-form-message'>Optional second WiFi network password</span>"

      // Active profile selector
      "<label>Active WiFi profile</label>"
      "<label class='pure-radio'><input type='radio' name='" FORM_NAME_WIFI_PROFILE "' value='1' %s>Profile&nbsp;1</label>"
      "<label class='pure-radio'><input type='radio' name='" FORM_NAME_WIFI_PROFILE "' value='2' %s>Profile&nbsp;2</label>"

      // Api key
      "<label for='" FORM_NAME_API_KEY "'>API key</label>"
      "<input type='text' name='" FORM_NAME_API_KEY "' id='" FORM_NAME_API_KEY "' value='%s'>"
      "<span class='pure-form-message'>"
      "Get your API key from <a target='_blank' href='https://api.safecast.org'>api.safecast.org</a>, Login -> Dashboard -> Retrieve your API key.<br>"
      "</span>"

      "<br>"
      "<button type='submit' class='pure-button pure-button-primary'>Save</button>"
      "</fieldset>"
      "</form>"
      "%s",
      settings.get_ap_password(),
      settings.get_device_id(),
      settings.get_wifi_ssid(),
      settings.get_wifi_password(),
      settings.get_wifi_ssid2(),
      settings.get_wifi_password2(),
      settings.get_wifi_profile_active()==1 ? "checked" : "",
      settings.get_wifi_profile_active()==2 ? "checked" : "",
      settings.get_api_key(),
      display_success ? success_message : ""
  );
}

const char* HttpPages::render_full_page(uint32_t device_id, const char* page_name, const char* content_format, ...) {
  sprintf(
      transmission_buffer,
      base_page_format_begin,
      page_name,
      device_id,
      local_resources,
      internet_access ? online_resources : fallback_resources,
      device_id
  );

  va_list args;
  va_start(args, content_format);
  vsprintf(
      &transmission_buffer[strlen(transmission_buffer)],
      content_format,
      args
  );
  va_end(args);

  sprintf(
      &transmission_buffer[strlen(transmission_buffer)],
      base_page_format_end
  );

  return transmission_buffer;
}

char HttpPages::transmission_buffer[] = "";

const char* HttpPages::pure_js =
    "(function (w,d){const a='active',l=d.getElementById('layout'),m=d.getElementById('menu'),n=d"
    ".getElementById('menuLink'),c=d.getElementById('main'),tc=(e,b)=>{const r=e.className.split("
    "/\\s+/),p=r.length;let i=0;while (i < p){if(r[i]===b){r.splice(i,1);break;}i++;}if(i===p){r."
    "push(b);}e.className=r.join(' ');},ta=(e)=>{e.preventDefault();tc(l,a);tc(m,a);tc(n,a);};n.o"
    "nclick=(e)=>ta(e);c.onclick=(e)=>m.className.indexOf(a)!==-1 && ta(e);}(this,this.document));";

/**
 *
 */
bool HttpPages::internet_access = false;

/**
 * Gzipped pure css library
 * https://purecss.io/
 */
const uint8_t HttpPages::pure_css[PURE_CSS_SIZE] = {
    0x1f, 0x8b, 0x08, 0x08, 0x56, 0xa2, 0xec, 0x5c, 0x00, 0x03, 0x70, 0x75, 0x72, 0x65, 0x2d, 0x6d,
    0x69, 0x6e, 0x2e, 0x63, 0x73, 0x73, 0x00, 0xed, 0x1b, 0x6b, 0x8f, 0xe3, 0xb6, 0xf1, 0xfb, 0xfd,
    0x0a, 0xe5, 0x0e, 0x07, 0xdc, 0x1e, 0x24, 0xaf, 0x2c, 0x3f, 0x57, 0x42, 0x82, 0x26, 0xcd, 0xa5,
    0x4d, 0x91, 0x06, 0x05, 0xd2, 0x2f, 0xc5, 0x65, 0x0b, 0xd0, 0x12, 0x6d, 0xab, 0xab, 0x17, 0x24,
    0x79, 0x1f, 0xe7, 0xfa, 0xbf, 0x77, 0xf8, 0x90, 0x34, 0x7c, 0xc8, 0xf6, 0xa6, 0x45, 0xd1, 0x0f,
    0x8d, 0x73, 0x77, 0x12, 0x39, 0x1c, 0x0e, 0xe7, 0xc5, 0x99, 0x21, 0x75, 0xfb, 0xf1, 0xab, 0x37,
    0x7f, 0x39, 0xd4, 0xd4, 0x79, 0x9c, 0x4e, 0xfc, 0x89, 0xff, 0xe6, 0xf7, 0x65, 0xf5, 0x52, 0xa7,
    0xbb, 0x7d, 0xeb, 0x04, 0xfe, 0x74, 0xe6, 0xfc, 0x8d, 0xec, 0xcb, 0xf2, 0xab, 0x37, 0x3f, 0xa5,
    0x31, 0x2d, 0x1a, 0x9a, 0x38, 0x87, 0x22, 0xa1, 0xb5, 0xd3, 0xee, 0xa9, 0xf3, 0xdd, 0x2f, 0xdf,
    0x3b, 0xb2, 0x79, 0xf2, 0x66, 0xdf, 0xb6, 0x55, 0x13, 0xde, 0xde, 0xee, 0xd2, 0x76, 0x7f, 0xd8,
    0x4c, 0xe2, 0x32, 0xbf, 0x7d, 0x61, 0x23, 0x6f, 0x2b, 0x40, 0x7d, 0xbb, 0xc9, 0xca, 0xcd, 0x6d,
    0x4e, 0x9a, 0x96, 0xd6, 0xb7, 0x3f, 0xfd, 0xf8, 0xfb, 0x4f, 0x3f, 0xff, 0xf2, 0x69, 0x92, 0x27,
    0x6f, 0x3e, 0xde, 0xbe, 0xb9, 0x85, 0xd9, 0x8b, 0xb2, 0xce, 0x49, 0x96, 0x7e, 0xa1, 0x93, 0xb8,
    0x69, 0x9c, 0xc7, 0xbf, 0xcf, 0x26, 0xbe, 0xf3, 0x4f, 0xe7, 0xcf, 0x3f, 0xfe, 0xb5, 0x43, 0x0f,
    0x6f, 0x80, 0x77, 0x92, 0x96, 0xb7, 0x3d, 0x28, 0x22, 0xf3, 0x43, 0x7c, 0xe3, 0xfc, 0x9c, 0xc6,
    0x65, 0x46, 0x1a, 0xe7, 0x0f, 0x24, 0xcb, 0xc8, 0x6e, 0x0f, 0x14, 0x92, 0x22, 0x71, 0xfe, 0x54,
    0x16, 0xa4, 0xdd, 0x93, 0xc2, 0xf9, 0x99, 0x92, 0x4c, 0xce, 0xe6, 0x68, 0xb3, 0xc1, 0x64, 0x93,
    0x99, 0x6d, 0xba, 0x6e, 0x19, 0x05, 0xe5, 0xa8, 0x6f, 0xd5, 0x71, 0x1f, 0x6f, 0x27, 0x6c, 0x65,
    0xde, 0xe6, 0xd0, 0xb6, 0x65, 0x11, 0x6e, 0xcb, 0xf8, 0xd0, 0xb8, 0x24, 0x24, 0x71, 0x9b, 0x3e,
    0x52, 0x78, 0xd8, 0x97, 0x8f, 0xb4, 0x3e, 0x96, 0x87, 0x36, 0x4b, 0x0b, 0x1a, 0xfa, 0x27, 0x01,
    0xdd, 0x92, 0x4d, 0x46, 0x5d, 0xfe, 0xf7, 0x71, 0x53, 0xd6, 0xc0, 0x49, 0x0f, 0x90, 0x67, 0xa4,
    0x6a, 0x68, 0xd8, 0x3d, 0x44, 0xb2, 0xa3, 0xa9, 0x48, 0x9c, 0x16, 0x3b, 0x18, 0xbb, 0x6f, 0xf3,
    0xec, 0xb8, 0x2d, 0x8b, 0xd6, 0xdb, 0x92, 0x3c, 0xcd, 0x5e, 0xc2, 0x86, 0x14, 0x8d, 0xd7, 0xd0,
    0x3a, 0xdd, 0x46, 0x5e, 0xde, 0x78, 0x2d, 0x7d, 0x6e, 0xbd, 0x06, 0x28, 0xf3, 0x48, 0xf2, 0x8f,
    0x43, 0xd3, 0x86, 0x53, 0xdf, 0x7f, 0x1f, 0x79, 0x4f, 0x74, 0xf3, 0x90, 0xb6, 0xf6, 0xde, 0xd3,
    0xa6, 0x4c, 0x5e, 0x8e, 0x39, 0xa9, 0x77, 0x69, 0x01, 0x33, 0x90, 0xba, 0x4d, 0x63, 0xa0, 0x8c,
    0x34, 0x69, 0x42, 0xdd, 0x84, 0xb6, 0x24, 0xcd, 0x1a, 0x77, 0x9b, 0xee, 0x62, 0x52, 0xb5, 0x69,
    0x59, 0xb0, 0x47, 0xa0, 0xdf, 0xdd, 0x96, 0x25, 0x88, 0xd0, 0xdd, 0x53, 0x92, 0xb0, 0x7f, 0x76,
    0x75, 0x79, 0xa8, 0xdc, 0x9c, 0xa4, 0x85, 0x9b, 0xd3, 0xe2, 0xe0, 0x16, 0xe4, 0xd1, 0x6d, 0x68,
    0xcc, 0x47, 0x34, 0x87, 0x1c, 0xd0, 0xbf, 0x1c, 0x93, 0xb4, 0xa9, 0x32, 0xf2, 0x12, 0x82, 0x0a,
    0xc4, 0x0f, 0x27, 0x72, 0x48, 0xd2, 0xd2, 0x8d, 0x49, 0xf1, 0x48, 0x1a, 0xb7, 0xaa, 0xcb, 0x5d,
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
    0x02, 0x21, 0x25, 0x76, 0xb6, 0xb7, 0xb0, 0xb9, 0xb1, 0x0e, 0x08, 0x01, 0xc7, 0x71, 0xe0, 0x38,
    0x0e, 0x00, 0xc0, 0xb2, 0x2c, 0x00, 0x80, 0x6d, 0xdb, 0x07, 0x2b, 0x08, 0xa9, 0xf0, 0x6e, 0xf6,
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
};
