Safecast/bGeigieZen/designs/Idea for coloring buttons.png

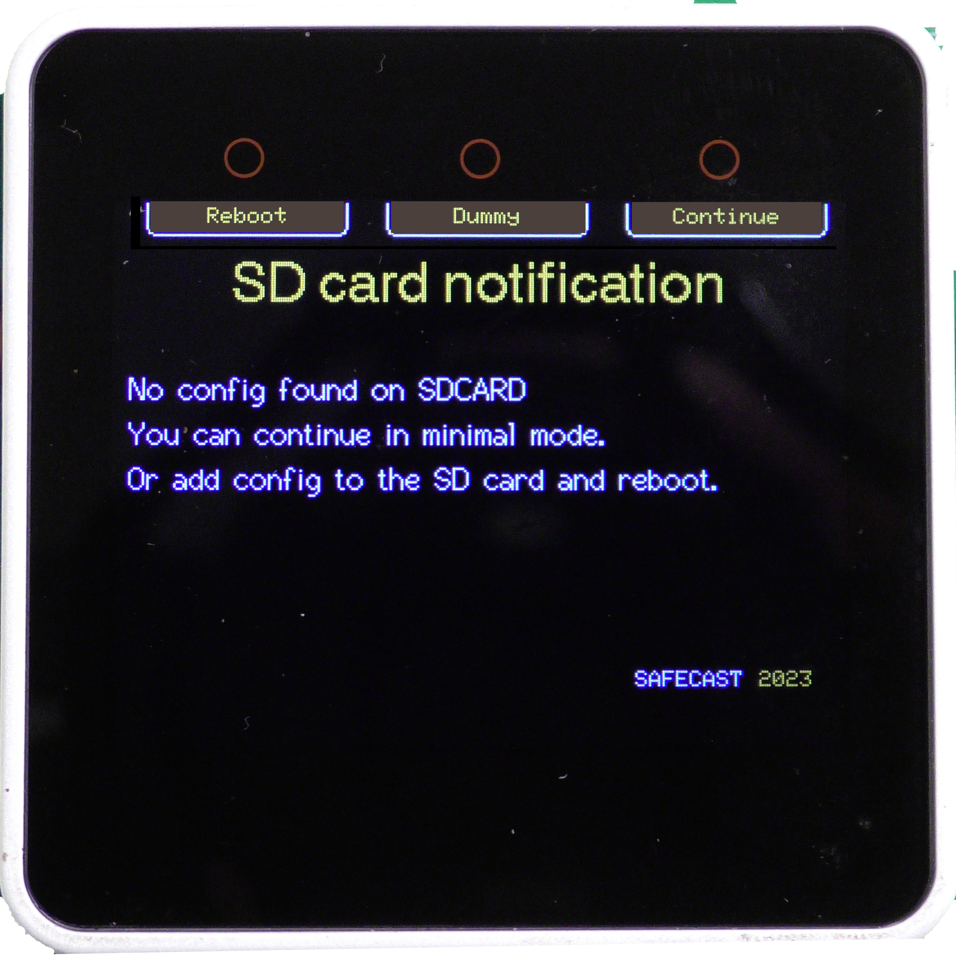
designs/Idea for coloring buttons.png
